booherbg/tedxfargo-charge-sign/docs/img/lens-matrix-clear.png

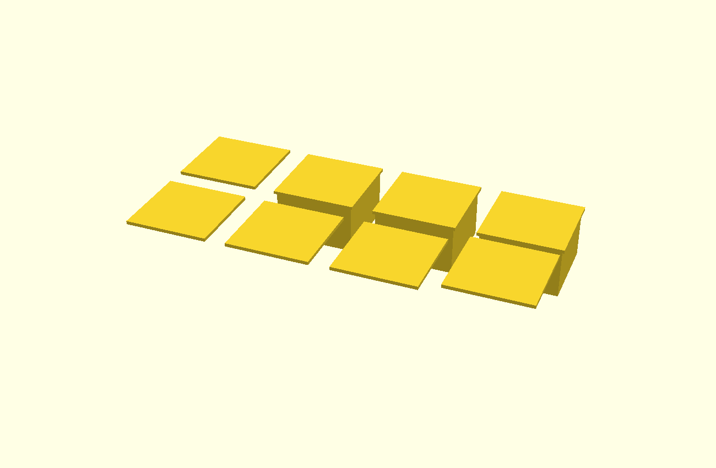
docs/img/lens-matrix-clear.png
