booherbg/tedxfargo-charge-sign/docs/img/lens-matrix-white.png

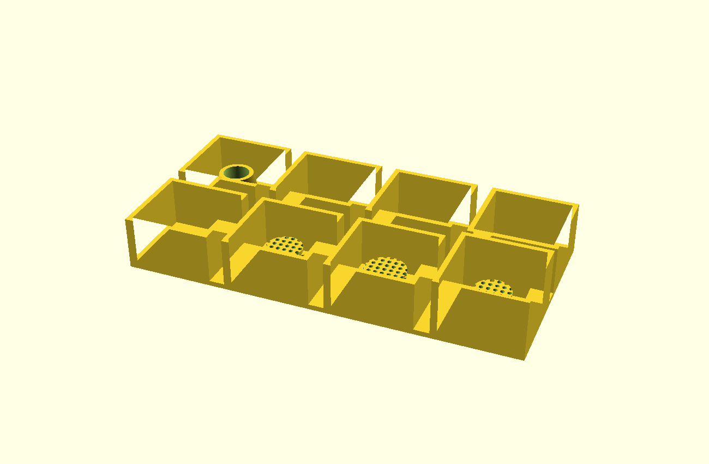
docs/img/lens-matrix-white.png
