booherbg/tedxfargo-charge-sign/docs/img/mockup-cap250-vs-squeezedH.png

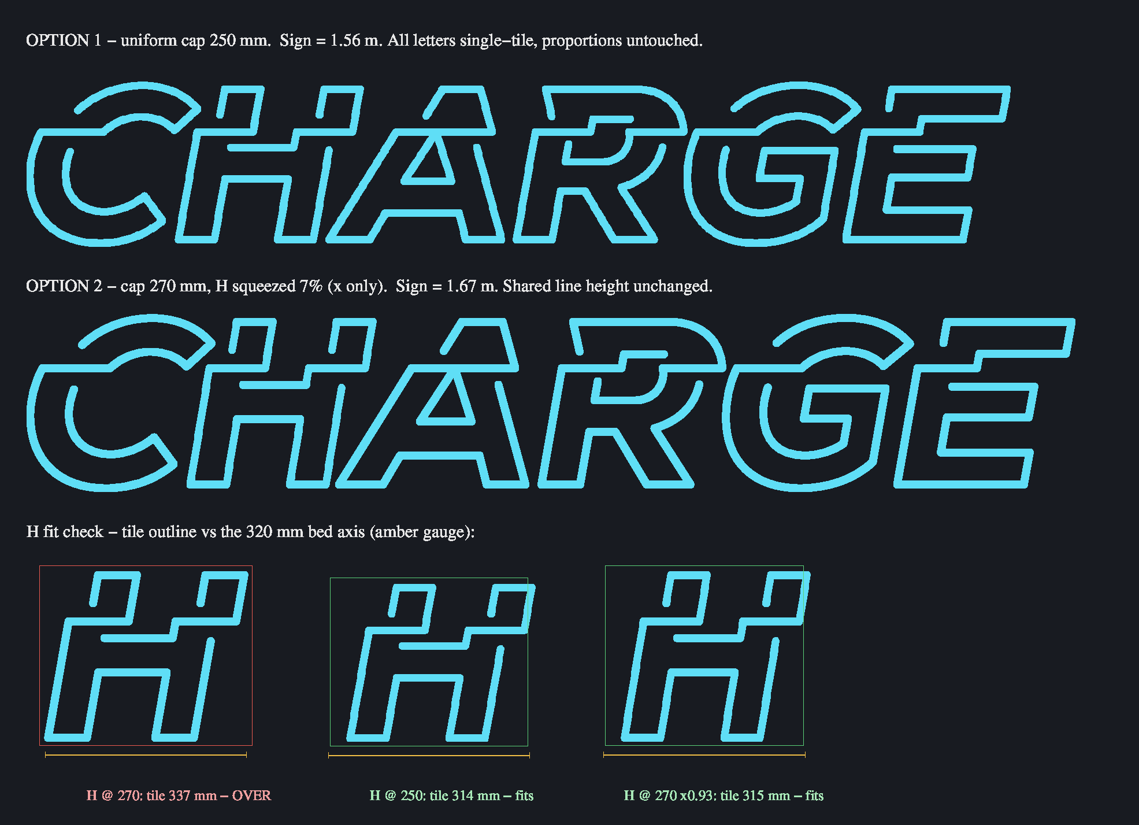
docs/img/mockup-cap250-vs-squeezedH.png
