booherbg/tedxfargo-charge-sign/sign-preview/c_thin.png

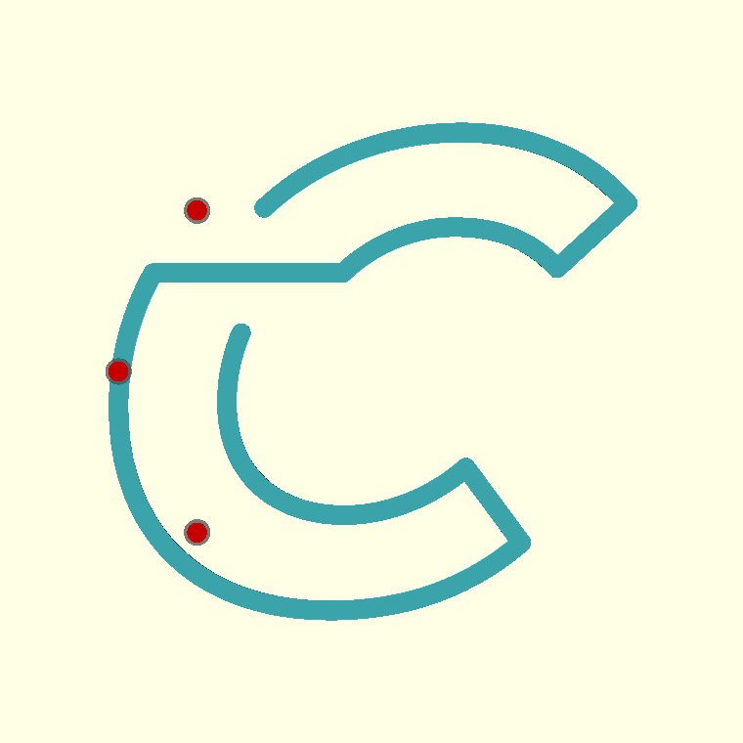
sign-preview/c_thin.png
