booherbg/tedxfargo-charge-sign/sign-preview/charge.png

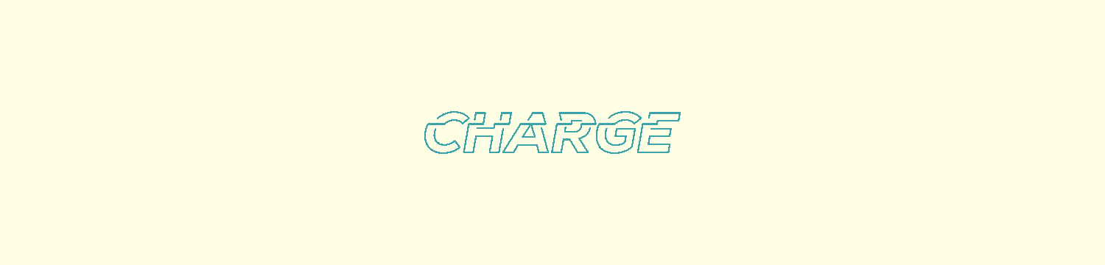
sign-preview/charge.png
