booherbg/tedxfargo-charge-sign/src/parts/bolt2_white.scad

// Integrated bolt v2 — WHITE shell (filament 1). Pair with bolt2_clear -> 3MF.
include <../config.scad>
include <../collar.scad>
include <../bolt.scad>
bolt_shell();
