booherbg/tedxfargo-charge-sign/src/parts/bolt_lens.scad

// Build target: lightning-bolt lens (bolt-shaped diffuser + locating lip).
// Print face-down (flange on bed), lip up; flip in use. Try it in white.
include <../config.scad>
include <../collar.scad>
include <../bolt.scad>
bolt_lens();
