booherbg/tedxfargo-charge-sign/src/parts/bolt_lens_v2_clear.scad

// V2 CLEAR part: clear center stripe + body + lip (edges removed). filament 2.
include <../config.scad>
include <../collar.scad>
include <../bolt.scad>
bolt_lens_v2_clear();
