booherbg/tedxfargo-charge-sign/src/parts/bolt_lens_v2_white.scad

// V2 WHITE part: white EDGES on the viewer/bed face. filament 1.
include <../config.scad>
include <../collar.scad>
include <../bolt.scad>
bolt_lens_v2_white();
