booherbg/tedxfargo-charge-sign/src/parts/bolt_piece.scad

// One element-6 bolt-board plate, one color body. Same cross-section as letters.
//   openscad -D PIECE=<1|2|3|4> -D COL=<1|2|3> -o out.stl src/parts/bolt_piece.scad
//   PIECE: 1 bottom-left, 2 bottom-right, 3 top-left, 4 top-right (bb_plates).
//   COL: 1 black, 2 white, 3 clear.
// CONTINUOUS MODE: channels cross the plate joints (the clip cuts them flush;
// butting plates continue the channel). Pixels/collars are kept off the seams
// by boltboard.py. Fuzz: fuzz_board_global.dat (dead-banded, board-centered).
include <../config.scad>
include <../collar.scad>
include <board_layout.scad>

PIECE = 1;
COL   = 1;

pb_ch_in    = 18;
pb_wall_wh  = 0.8;
pb_wall_bk  = 1.2;
pb_band_out = pb_ch_in + 2*(pb_wall_wh + pb_wall_bk);
pb_liner_t  = 0.4;
pb_wall_h   = dome_clear + 15;
pb_lens_t   = 1.2;
pb_fuse     = 0.1;
pb_seam     = 0.06;
pb_scr_d    = 4.5;
pb_tie_d    = 3.2;

pr = bb_plates[PIECE-1];               // [x0, x1, y0, y1]
x0 = pr[0]; x1 = pr[1]; y0 = pr[2]; y1 = pr[3];
// shave pb_seam off interior edges only (butt-joint clearance)
cx0 = x0 + (x0 > 0.1 ? pb_seam : 0);
cx1 = x1 - (x1 < bb_face[0] - 0.1 ? pb_seam : 0);
cy0 = y0 + (y0 > 0.1 ? pb_seam : 0);
cy1 = y1 - (y1 < bb_face[1] - 0.1 ? pb_seam : 0);

pxs  = [for (p = bb_px)  if (p[0] >= x0 && p[0] < x1 && p[1] >= y0 && p[1] < y1) p];
scrs = [for (p = bb_scr) if (p[0] >= x0 && p[0] < x1 && p[1] >= y0 && p[1] < y1) p];
ties = [for (p = bb_tie) if (p[0] >= x0 && p[0] < x1 && p[1] >= y0 && p[1] < y1) p];
// on-seam pixels (collar lives in the seam strap): Ø13 barrel bite, split
// across the mating plate edges — expanded bounds so BOTH plates cut theirs
bts  = [for (p = bb_bite) if (p[0] >= x0 - 10 && p[0] < x1 + 10
                           && p[1] >= y0 - 10 && p[1] < y1 + 10) p];
pb_bite_d = 13.0;

module path_stroke(pts, w) {
    for (i = [0 : len(pts)-2])
        hull() { translate(pts[i]) circle(d=w); translate(pts[i+1]) circle(d=w); }
}
module band(w) { for (p = bb_paths) path_stroke(p, w); }
module clip() {                       // plate window with seam clearance
    intersection() {
        children(0);
        translate([cx0, cy0, -1]) cube([cx1 - cx0, cy1 - cy0, 60]);
    }
}

module body_black() {
    clip() union() {
        difference() {
            linear_extrude(plate_t) square([bb_face[0], bb_face[1]]);
            for (p = pxs)  translate([p[0], p[1], -0.1]) cylinder(h=plate_t+0.2, d=collar_od);
            for (p = scrs) translate([p[0], p[1], -0.1]) cylinder(h=plate_t+0.2, d=pb_scr_d);
            for (p = ties) translate([p[0], p[1], -0.1]) cylinder(h=plate_t+0.2, d=pb_tie_d);
            for (p = bts)  translate([p[0], p[1], -0.1]) cylinder(h=plate_t+0.2, d=pb_bite_d);
            translate([(x0+x1)/2, y0 + 14, -0.1]) linear_extrude(0.9) mirror([1,0,0])
                text(str("B", PIECE), size=8, halign="center", valign="center");
        }
        translate([0,0,plate_t]) linear_extrude(pb_wall_h)
            difference() { band(pb_band_out); band(pb_band_out - 2*pb_wall_bk); }
    }
}
module body_white() {
    clip() union() {
        difference() {
            translate([0,0,plate_t]) linear_extrude(pb_liner_t) band(pb_ch_in);
            for (p = pxs) translate([p[0], p[1], -0.1])
                cylinder(h=plate_t+pb_liner_t+0.2, d=pixel_through);
            for (p = bts) translate([p[0], p[1], -0.1])
                cylinder(h=plate_t+pb_liner_t+0.2, d=pb_bite_d);
        }
        translate([0,0,plate_t]) linear_extrude(pb_wall_h)
            difference() { band(pb_ch_in + 2*pb_wall_wh); band(pb_ch_in); }
        for (p = pxs) place_collar(p[0], p[1]);
    }
}
module body_clear() {
    z0  = plate_t + pb_wall_h - pb_fuse;
    top = plate_t + pb_wall_h + pb_lens_t;
    // per-plate CROP of the one global fuzz field (identical values -> texture
    // continuous across the joints; cropping keeps surface() meshes small)
    clip() union() {
        translate([0,0,z0]) linear_extrude(top - z0) band(pb_band_out);
        intersection() {
            translate([bb_fuzz_ctr[PIECE-1][0], bb_fuzz_ctr[PIECE-1][1], top-0.1504])
                scale([0.6667,0.6667,1])  // V8: dat sampled at cell/3 = 0.667mm
                surface(file = str("fuzz_board_p", PIECE, ".dat"), center = true, convexity = 8);
            translate([0,0,top-0.3]) linear_extrude(3) band(pb_band_out);
        }
    }
}

if (COL == 1) body_black();
else if (COL == 2) body_white();
else body_clear();
