booherbg/tedxfargo-charge-sign/src/parts/bolt_shell.scad

// Build target: lightning-bolt shell (channel + merged collars). Print rear-down.
include <../config.scad>
include <../collar.scad>
include <../bolt.scad>
bolt_shell();
