booherbg/tedxfargo-charge-sign/src/parts/boltx_data.scad

// AUTO-GENERATED by tools/centerline.py — do not hand-edit
// bolt_element6.pgm @ cap 270mm (ref ): centerline bbox 354.8 x 493.1 mm, tube ~12.3mm wide
// 3 tube segment(s), 1497+370+589 mm, 127 pixels @ 20.0mm pitch
BOLTX_paths = [
    [[10.89,320.45],[11.86,316.57],[12.94,312.72],[14.97,309.29],[17.16,305.95],[19.38,302.62],[21.62,299.31],[23.87,296.00],[26.14,292.71],[28.39,289.40],[30.68,286.12],[32.91,282.80],[35.24,279.55],[37.47,276.24],[39.77,272.97],[42.04,269.67],[44.32,266.38],[46.59,263.10],[48.85,259.80],[51.16,256.53],[53.39,253.22],[55.72,249.96],[57.94,246.64],[60.27,243.39],[62.51,240.07],[64.82,236.81],[67.06,233.50],[69.36,230.23],[71.63,226.94],[73.90,223.64],[76.19,220.37],[78.44,217.06],[80.75,213.80],[83.02,210.51],[85.31,207.23],[87.56,203.92],[89.87,200.66],[92.12,197.35],[94.43,194.09],[96.66,190.77],[98.99,187.52],[101.22,184.20],[103.53,180.94],[105.78,177.63],[107.80,174.20],[108.66,170.32],[107.66,166.45],[105.63,163.02],[103.35,159.73],[101.12,156.41],[98.89,153.10],[96.64,149.79],[94.41,146.47],[92.14,143.17],[89.93,139.84],[87.70,136.52],[85.44,133.23],[83.20,129.92],[80.92,126.62],[78.71,123.30],[76.49,119.97],[74.26,116.65],[72.01,113.34],[69.77,110.03],[67.49,106.74],[65.27,103.42],[63.05,100.09],[60.83,96.76],[58.56,93.47],[56.32,90.16],[54.05,86.87],[51.83,83.54],[49.62,80.21],[47.39,76.89],[45.13,73.58],[42.85,70.30],[40.62,66.99],[38.40,63.66],[36.18,60.33],[33.95,57.01],[31.65,53.74],[29.39,50.44],[27.18,47.11],[24.96,43.78],[22.74,40.45],[20.52,37.12],[18.29,33.81],[16.05,30.49],[13.82,27.17],[11.59,23.86],[9.35,20.54],[7.12,17.23],[4.92,13.88],[2.76,10.51],[1.53,6.74],[0.55,2.87],[2.11,0.00],[6.11,0.00],[10.11,0.00],[14.10,0.00],[18.10,0.00],[22.10,0.00],[26.10,0.00],[30.10,0.00],[34.10,0.00],[38.10,0.00],[42.10,0.00],[46.10,0.00],[50.10,0.00],[54.10,0.00],[58.10,0.00],[62.10,0.00],[66.09,0.00],[70.09,0.00],[74.09,0.00],[78.09,0.00],[82.09,0.00],[86.09,0.00],[90.09,0.00],[94.08,0.25],[98.07,0.28],[102.07,0.28],[106.07,0.28],[110.03,0.69],[113.09,3.10],[115.52,6.28],[117.74,9.60],[119.77,13.05],[121.82,16.48],[123.87,19.92],[125.92,23.35],[127.95,26.79],[130.00,30.23],[132.03,33.67],[134.07,37.11],[136.11,40.55],[138.15,43.99],[140.19,47.43],[142.23,50.87],[144.29,54.30],[146.32,57.75],[148.37,61.18],[150.41,64.62],[152.47,68.05],[154.50,71.50],[156.51,74.95],[158.55,78.39],[160.60,81.83],[162.64,85.26],[164.69,88.70],[166.74,92.13],[169.41,95.02],[173.18,96.05],[176.75,94.36],[179.05,91.13],[181.11,87.70],[183.19,84.29],[185.30,80.88],[187.36,77.46],[189.44,74.04],[191.50,70.61],[193.56,67.19],[195.62,63.76],[197.68,60.33],[199.73,56.90],[201.78,53.47],[203.84,50.04],[205.91,46.61],[207.97,43.19],[210.03,39.76],[212.09,36.33],[214.15,32.90],[216.21,29.48],[218.27,26.05],[220.33,22.62],[222.39,19.19],[224.45,15.76],[226.50,12.33],[228.57,8.91],[230.71,5.53],[233.04,2.28],[236.63,0.78],[240.61,0.55],[244.61,0.55],[248.61,0.55],[252.61,0.55],[256.61,0.55],[260.61,0.55],[264.61,0.55],[268.61,0.55],[272.61,0.55],[276.61,0.55],[280.61,0.55],[284.61,0.55],[288.60,0.55],[292.60,0.55],[296.60,0.55],[300.60,0.55],[304.60,0.55],[308.60,0.55],[312.60,0.55],[316.60,0.55],[320.60,0.55],[324.60,0.55],[328.60,0.55],[332.58,0.78],[336.58,0.83],[340.58,0.83],[344.58,0.83],[348.58,0.83],[352.58,0.84],[354.44,3.65],[353.48,7.53],[352.20,11.29],[350.03,14.64],[347.83,17.99],[345.61,21.31],[343.39,24.64],[341.18,27.97],[338.94,31.28],[336.70,34.60],[334.43,37.89],[332.18,41.19],[329.94,44.51],[327.67,47.80],[325.39,51.09],[323.15,54.40],[320.86,57.68],[318.61,60.99],[316.35,64.28],[314.05,67.56],[311.83,70.88],[309.56,74.17],[307.28,77.46],[305.05,80.78],[302.78,84.07],[300.49,87.35],[298.27,90.68],[296.00,93.97],[293.70,97.24],[291.49,100.57],[289.24,103.87],[286.94,107.15],[284.71,110.47],[282.44,113.76],[280.15,117.04],[277.92,120.36],[275.65,123.65],[273.36,126.93],[271.15,130.26],[268.83,133.52],[266.58,136.83],[264.36,140.15],[262.09,143.44],[259.81,146.72],[257.58,150.05],[255.33,153.35],[253.02,156.62],[250.81,159.95],[248.58,163.27],[246.51,166.68],[245.73,170.58],[246.68,174.44],[248.70,177.88],[250.95,181.18],[253.26,184.45],[255.48,187.77],[257.72,191.08],[260.04,194.34],[262.25,197.67],[264.54,200.95],[266.82,204.24],[269.04,207.56],[271.34,210.84],[273.60,214.13],[275.85,217.44],[278.15,220.71],[280.38,224.03],[282.66,227.31],[284.95,230.60],[287.17,233.92],[289.44,237.21],[291.72,240.50],[293.94,243.82],[296.23,247.10],[298.51,250.39],[300.74,253.71],[303.03,256.98],[305.29,260.28],[307.53,263.60],[309.82,266.88],[312.07,270.18],[314.31,273.49],[316.61,276.76],[318.85,280.08],[321.10,283.38],[323.39,286.67],[325.62,289.98],[327.91,293.26],[330.17,296.56],[332.43,299.86],[334.65,303.18],[336.88,306.51],[339.09,309.84],[341.13,313.26],[342.16,317.12],[343.07,321.01],[340.27,322.79],[336.27,322.79],[332.27,322.79],[328.27,322.79],[324.27,322.79],[320.27,322.79],[316.27,322.79],[312.27,322.79],[308.27,322.79],[304.27,322.79],[300.29,323.07],[296.29,323.07],[292.29,323.07],[288.29,323.11],[284.40,322.66],[281.04,320.65],[278.73,317.39],[276.44,314.11],[274.16,310.82],[271.91,307.51],[269.67,304.20],[267.42,300.89],[265.20,297.57],[262.97,294.25],[260.75,290.92],[258.53,287.60],[256.32,284.27],[254.03,280.99],[251.81,277.66],[249.59,274.33],[247.38,271.00],[245.16,267.67],[242.94,264.35],[240.72,261.02],[238.50,257.70],[236.25,254.39],[234.01,251.08],[231.79,247.75],[229.56,244.43],[227.35,241.10],[225.06,237.82],[222.85,234.48],[220.63,231.16],[218.41,227.83],[216.20,224.50],[213.97,221.18],[211.76,217.85],[209.54,214.52],[207.32,211.19],[205.10,207.87],[202.84,204.57],[200.60,201.25],[198.35,197.95],[196.09,194.65],[193.88,191.31],[191.67,187.99],[189.44,184.66],[187.22,181.33],[184.98,178.02],[182.76,174.70],[180.51,171.39],[178.29,168.07],[176.04,164.76],[173.80,161.44],[171.57,158.13],[169.36,154.79],[167.11,151.48],[164.88,148.17],[162.64,144.86]],
    [[140.38,126.66],[140.65,130.63],[141.04,134.60],[141.69,138.53],[142.59,142.41],[143.56,146.28],[144.47,150.16],[145.41,154.03],[146.33,157.91],[147.27,161.79],[148.20,165.67],[149.12,169.54],[150.01,173.43],[150.87,177.32],[151.83,181.19],[152.74,185.07],[153.67,188.95],[154.59,192.83],[155.52,196.71],[156.43,200.59],[157.37,204.46],[158.29,208.34],[159.25,212.21],[160.14,216.10],[161.10,219.97],[162.02,223.85],[162.93,227.73],[163.87,231.60],[164.81,235.48],[165.72,239.36],[166.64,243.24],[167.61,247.11],[168.53,250.98],[169.45,254.86],[170.39,258.74],[171.32,262.62],[172.23,266.50],[173.15,270.38],[174.11,274.25],[175.00,278.13],[175.92,282.01],[176.83,285.89],[177.70,289.78],[178.65,293.66],[179.55,297.54],[180.43,301.43],[181.39,305.30],[182.32,309.17],[183.04,313.09],[183.44,317.06],[183.00,320.85],[179.32,321.97],[175.33,321.97],[171.35,321.97],[167.36,321.97],[163.37,321.97],[159.38,321.97],[155.40,321.97],[151.41,321.97],[147.42,321.97],[143.44,321.97],[139.45,321.97],[135.46,321.97],[131.47,321.97],[127.49,321.97],[123.50,321.97],[119.51,321.97],[115.53,321.87],[111.55,321.69],[107.56,321.69],[103.58,321.80],[99.60,321.97],[95.62,321.97],[91.63,321.97],[87.64,321.97],[83.65,321.97],[79.67,321.97],[75.71,322.14],[71.79,322.23],[67.81,321.97],[63.82,321.97],[59.84,321.97],[55.85,321.97],[51.86,321.97],[47.88,321.97],[43.89,321.97],[39.90,321.97],[35.91,321.97],[31.93,321.97],[27.94,321.97],[23.95,321.97],[19.97,321.97],[15.98,321.97],[11.99,321.97]],
    [[287.16,324.31],[288.17,328.18],[289.14,332.05],[290.81,335.64],[293.00,338.98],[295.20,342.31],[297.41,345.65],[299.63,348.97],[301.85,352.29],[304.09,355.60],[306.32,358.91],[308.47,362.28],[310.48,365.73],[311.45,369.60],[312.33,373.50],[309.68,375.44],[305.68,375.44],[301.68,375.44],[297.69,375.44],[293.69,375.44],[289.70,375.44],[285.70,375.44],[281.71,375.44],[277.71,375.44],[273.72,375.44],[269.72,375.44],[265.73,375.44],[261.73,375.44],[257.73,375.44],[253.74,375.44],[249.74,375.44],[245.75,375.44],[241.75,375.44],[237.77,375.17],[233.78,375.17],[229.78,375.17],[225.79,375.17],[221.80,375.29],[220.68,378.46],[221.57,382.36],[222.67,386.18],[224.67,389.64],[226.71,393.07],[228.76,396.50],[230.81,399.93],[232.86,403.36],[234.90,406.79],[236.95,410.22],[238.99,413.66],[241.01,417.10],[243.05,420.54],[245.10,423.97],[247.16,427.39],[249.22,430.82],[251.26,434.25],[253.31,437.68],[255.37,441.11],[257.41,444.54],[259.46,447.97],[261.50,451.40],[263.56,454.83],[265.60,458.26],[267.62,461.71],[269.68,465.13],[271.67,468.60],[273.73,472.02],[275.76,475.46],[277.82,478.89],[279.78,482.36],[280.84,486.20],[281.76,490.09],[280.42,493.07],[276.42,493.15],[272.43,493.15],[268.43,493.15],[264.44,493.15],[260.44,493.15],[256.45,493.15],[252.45,493.15],[248.46,493.15],[244.46,493.15],[240.47,493.15],[236.47,493.15],[232.47,493.15],[228.48,493.15],[224.48,493.15],[220.49,493.15],[216.49,493.15],[212.50,493.15],[208.50,493.15],[204.51,493.15],[200.51,493.15],[196.52,493.15],[192.52,493.15],[188.52,493.15],[184.53,493.15],[180.53,493.15],[176.54,493.15],[172.54,493.14],[168.57,492.83],[164.70,491.89],[162.01,489.12],[160.08,485.62],[158.16,482.12],[156.25,478.61],[154.35,475.10],[152.44,471.59],[150.52,468.08],[148.59,464.59],[146.69,461.07],[144.75,457.58],[142.86,454.06],[140.96,450.54],[139.03,447.05],[137.13,443.53],[135.23,440.02],[133.30,436.52],[131.40,433.00],[129.48,429.50],[127.57,425.99],[125.66,422.48],[123.74,418.98],[121.83,415.47],[119.93,411.96],[118.02,408.44],[116.10,404.94],[114.19,401.43],[112.27,397.93],[110.36,394.42],[108.45,390.91],[106.53,387.41],[104.62,383.90],[102.71,380.39],[100.80,376.88],[98.90,373.36],[96.98,369.86],[95.08,366.34],[93.17,362.84],[91.27,359.32],[89.36,355.82],[87.43,352.32],[85.53,348.80],[83.63,345.29],[81.73,341.77],[79.84,338.25],[77.97,334.72],[76.55,331.01],[75.66,327.12],[74.84,323.21]]
];
BOLTX_closed = [0, 0, 0];
BOLTX_pixels = [[10.89,320.45],[19.38,302.62],[30.68,286.12],[42.04,269.67],[53.39,253.22],[64.82,236.81],[76.19,220.37],[87.56,203.92],[98.99,187.52],[108.66,170.32],[98.89,153.10],[87.70,136.52],[76.49,119.97],[65.27,103.42],[54.05,86.87],[42.85,70.30],[31.65,53.74],[20.52,37.12],[9.35,20.54],[0.55,2.87],[18.10,0.00],[38.10,0.00],[58.10,0.00],[78.09,0.00],[98.07,0.28],[115.52,6.28],[125.92,23.35],[136.11,40.55],[146.32,57.75],[156.51,74.95],[166.74,92.13],[181.11,87.70],[191.50,70.61],[201.78,53.47],[212.09,36.33],[222.39,19.19],[233.04,2.28],[252.61,0.55],[272.61,0.55],[292.60,0.55],[312.60,0.55],[332.58,0.78],[352.58,0.84],[347.83,17.99],[336.70,34.60],[325.39,51.09],[314.05,67.56],[302.78,84.07],[291.49,100.57],[280.15,117.04],[268.83,133.52],[257.58,150.05],[246.51,166.68],[253.26,184.45],[264.54,200.95],[275.85,217.44],[287.17,233.92],[298.51,250.39],[309.82,266.88],[321.10,283.38],[332.43,299.86],[342.16,317.12],[328.27,322.79],[308.27,322.79],[288.29,323.11],[274.16,310.82],[262.97,294.25],[251.81,277.66],[240.72,261.02],[229.56,244.43],[218.41,227.83],[207.32,211.19],[196.09,194.65],[184.98,178.02],[173.80,161.44],[162.64,144.86],[140.38,126.66],[143.47,145.87],[147.99,164.85],[152.43,183.86],[156.97,202.83],[161.52,221.81],[166.09,240.78],[170.63,259.76],[175.16,278.74],[179.60,297.74],[183.42,316.85],[167.99,321.97],[148.47,321.97],[128.96,321.97],[109.45,321.69],[89.95,321.97],[70.54,322.08],[51.02,321.97],[31.51,321.97],[11.99,321.97],[287.16,324.31],[295.06,342.09],[306.02,358.48],[310.47,375.40],[290.76,375.44],[271.05,375.44],[251.34,375.44],[231.65,375.17],[221.96,384.18],[231.63,401.30],[241.70,418.24],[251.80,435.17],[261.91,452.09],[271.94,469.06],[280.90,486.46],[268.43,493.15],[248.72,493.15],[229.01,493.15],[209.30,493.15],[189.59,493.15],[169.90,492.90],[157.02,480.01],[147.59,462.71],[138.14,445.41],[128.72,428.10],[119.30,410.78],[109.85,393.49],[100.42,376.18],[91.02,358.85],[81.60,341.54],[74.84,323.21]];
BOLTX_bbox = [354.77, 493.15];
