booherbg/tedxfargo-charge-sign/src/parts/cap_fit_0p1.scad

// Fit test: over-cap skirt clearance 0.1mm (2 dots). Middle.
include <../config.scad>
include <../collar.scad>
include <../bolt.scad>
cap_chunk(0.1, 2);
