booherbg/tedxfargo-charge-sign/src/parts/cap_fit_0p2.scad

// Fit test: over-cap skirt clearance 0.2mm (1 dot). Loosest of the three.
include <../config.scad>
include <../collar.scad>
include <../bolt.scad>
cap_chunk(0.2, 1);
