booherbg/tedxfargo-charge-sign/src/parts/collar_harness.scad

// Build target: collar A/B test tile (original vs chamfered v2).
include <../config.scad>
include <../collar.scad>
include <../collar_v2.scad>
include <../harness.scad>
collar_harness();
