booherbg/tedxfargo-charge-sign/src/parts/coupon_body.scad

// Build target: the stackup test coupon body.
include <../config.scad>
include <../collar.scad>
include <../diffuser.scad>
include <../coupon.scad>
coupon_body();
