booherbg/tedxfargo-charge-sign/src/parts/lens_fit_0p2.scad

// Fit test: inner-lens lip clearance 0.2mm (3 dots).
include <../config.scad>
include <../collar.scad>
include <../bolt.scad>
lens_chunk(0.2, 3, label="0.2");
