booherbg/tedxfargo-charge-sign/src/parts/lens_fit_0p3.scad

// Fit test: inner-lens lip clearance 0.3mm (2 dots).
include <../config.scad>
include <../collar.scad>
include <../bolt.scad>
lens_chunk(0.3, 2, label="0.3");
