booherbg/tedxfargo-charge-sign/src/parts/letter_C_data.scad

// AUTO-GENERATED by tools/centerline.py — do not hand-edit
// C.eps @ cap 270mm (ref H.eps): centerline bbox 285.9 x 270.9 mm, tube ~11.8mm wide
// 1 tube segment(s), 1161 mm, 69 pixels @ 17.0mm pitch
C_paths = [
    [[85.59,231.18],[88.75,233.62],[91.83,236.17],[94.99,238.61],[98.24,240.94],[101.55,243.17],[104.83,245.46],[108.27,247.48],[111.75,249.45],[115.22,251.42],[118.76,253.28],[122.29,255.15],[125.94,256.76],[129.60,258.37],[133.31,259.85],[137.10,261.13],[140.93,262.27],[144.72,263.53],[148.56,264.65],[152.39,265.78],[156.26,266.75],[160.16,267.61],[164.11,268.20],[168.06,268.85],[172.02,269.37],[175.97,269.95],[179.93,270.41],[183.90,270.76],[187.89,270.88],[191.88,270.88],[195.88,270.88],[199.88,270.88],[203.87,270.84],[207.84,270.42],[211.80,269.88],[215.74,269.29],[219.70,268.79],[223.62,268.09],[227.49,267.10],[231.38,266.15],[235.25,265.16],[239.02,263.84],[242.82,262.61],[246.52,261.12],[250.14,259.42],[253.75,257.72],[257.31,255.90],[260.73,253.85],[264.15,251.78],[267.51,249.62],[270.70,247.21],[273.86,244.77],[276.98,242.26],[279.99,239.64],[282.85,236.85],[284.95,233.53],[285.38,229.66],[283.75,226.06],[280.77,223.41],[277.88,220.64],[274.90,217.99],[271.97,215.28],[269.04,212.57],[266.06,209.91],[263.18,207.15],[260.16,204.53],[257.29,201.74],[254.28,199.12],[250.70,197.44],[246.78,197.49],[243.25,199.26],[240.23,201.88],[237.00,204.23],[233.67,206.42],[230.18,208.38],[226.65,210.25],[222.96,211.79],[219.20,213.13],[215.36,214.24],[211.51,215.31],[207.56,215.89],[203.61,216.46],[199.66,217.06],[195.66,217.06],[191.68,217.30],[187.71,217.06],[183.72,217.06],[179.76,216.53],[175.80,215.96],[171.87,215.26],[167.98,214.37],[164.17,213.18],[160.36,212.00],[156.66,210.49],[152.97,208.96],[149.41,207.15],[145.93,205.18],[142.51,203.12],[139.19,200.89],[135.94,198.56],[132.74,196.18],[129.66,193.64],[126.03,192.03],[122.10,191.47],[118.10,191.47],[114.10,191.47],[110.10,191.47],[106.11,191.47],[102.11,191.47],[98.11,191.47],[94.12,191.47],[90.12,191.47],[86.12,191.47],[82.13,191.47],[78.13,191.47],[74.13,191.47],[70.14,191.47],[66.14,191.47],[62.14,191.47],[58.14,191.47],[54.15,191.47],[50.15,191.47],[46.15,191.47],[42.16,191.47],[38.16,191.47],[34.16,191.47],[30.17,191.47],[26.17,191.47],[22.22,190.97],[18.70,189.26],[16.70,185.82],[14.94,182.23],[13.29,178.59],[11.72,174.92],[10.29,171.20],[9.07,167.39],[7.75,163.62],[6.50,159.83],[5.40,155.99],[4.39,152.12],[3.57,148.21],[2.83,144.28],[2.13,140.35],[1.59,136.39],[0.97,132.45],[0.44,128.49],[0.11,124.52],[0.00,120.53],[0.00,116.53],[0.00,112.53],[0.00,108.54],[0.40,104.57],[0.63,100.59],[1.14,96.63],[1.67,92.68],[2.23,88.74],[3.02,84.83],[3.86,80.92],[5.03,77.10],[6.28,73.30],[7.56,69.51],[8.84,65.73],[10.39,62.05],[12.13,58.45],[13.93,54.88],[15.92,51.42],[17.93,47.96],[20.32,44.76],[22.72,41.57],[25.16,38.41],[27.94,35.54],[30.56,32.52],[33.39,29.70],[36.41,27.08],[39.44,24.48],[42.66,22.12],[46.00,19.92],[49.36,17.76],[52.83,15.79],[56.39,13.98],[59.98,12.22],[63.61,10.55],[67.33,9.07],[71.05,7.63],[74.85,6.38],[78.70,5.31],[82.60,4.43],[86.50,3.59],[90.41,2.74],[94.34,2.03],[98.30,1.46],[102.25,0.99],[106.25,0.82],[110.21,0.44],[114.17,0.00],[118.17,0.00],[122.17,0.00],[126.16,0.00],[130.12,0.44],[134.09,0.81],[138.07,1.06],[142.04,1.45],[146.00,1.86],[149.95,2.46],[153.87,3.24],[157.78,4.08],[161.69,4.90],[165.60,5.74],[169.45,6.78],[173.29,7.90],[177.10,9.08],[180.81,10.56],[184.53,12.05],[188.20,13.61],[191.90,15.12],[195.49,16.88],[199.05,18.69],[202.61,20.50],[206.02,22.58],[209.38,24.75],[212.80,26.82],[216.09,29.08],[219.37,31.37],[222.54,33.80],[225.08,36.84],[225.26,40.74],[223.98,44.49],[221.54,47.65],[219.20,50.89],[216.80,54.09],[214.39,57.28],[212.09,60.54],[209.69,63.74],[207.29,66.93],[204.94,70.16],[202.56,73.38],[199.99,76.41],[196.23,77.62],[192.36,76.70],[188.99,74.62],[185.70,72.35],[182.36,70.16],[178.86,68.23],[175.33,66.37],[171.75,64.59],[168.15,62.85],[164.42,61.43],[160.67,60.03],[156.92,58.65],[153.06,57.63],[149.16,56.74],[145.24,56.02],[141.34,55.17],[137.37,54.75],[133.39,54.48],[129.41,54.26],[125.42,54.26],[121.45,54.64],[117.46,54.72],[113.52,55.38],[109.60,56.17],[105.70,57.04],[101.87,58.16],[98.15,59.63],[94.48,61.20],[90.92,63.01],[87.49,65.06],[84.23,67.35],[81.11,69.86],[78.24,72.64],[75.43,75.48],[72.99,78.64],[70.85,82.01],[68.88,85.49],[67.04,89.03],[65.60,92.76],[64.49,96.59],[63.35,100.41],[62.62,104.34],[62.07,108.29],[61.76,112.26],[61.48,116.23],[61.71,120.19],[61.76,124.18],[62.05,128.16],[62.64,132.11],[63.18,136.07],[63.94,139.99],[64.95,143.86],[66.03,147.70],[67.28,151.50],[68.53,155.29]]
];
C_closed = [0];
C_pixels = [[85.59,231.18],[99.16,241.56],[113.71,250.52],[129.01,258.10],[145.17,263.68],[161.73,267.85],[178.65,270.26],[195.70,270.88],[212.72,269.72],[229.50,266.64],[245.78,261.48],[260.97,253.67],[274.96,243.88],[285.56,231.09],[275.15,218.24],[262.61,206.63],[248.85,197.14],[234.48,205.85],[219.09,213.16],[202.39,216.66],[185.36,217.06],[168.47,214.57],[152.45,208.69],[137.81,199.89],[123.27,191.50],[106.17,191.47],[89.06,191.47],[71.96,191.47],[54.85,191.47],[37.75,191.47],[20.75,190.56],[12.23,176.17],[6.57,160.05],[2.66,143.42],[0.40,126.49],[0.00,109.42],[1.72,92.45],[5.44,75.81],[11.46,59.82],[20.07,45.09],[31.06,32.03],[44.18,21.12],[59.02,12.66],[74.90,6.36],[91.56,2.51],[108.51,0.49],[125.58,0.00],[142.56,1.51],[159.38,4.44],[175.95,8.64],[191.80,15.07],[206.88,23.10],[221.08,32.62],[222.00,47.04],[211.88,60.83],[201.67,74.54],[186.87,73.13],[172.01,64.71],[156.13,58.43],[139.40,55.06],[122.38,54.49],[105.53,57.07],[89.78,63.62],[76.54,74.34],[67.24,88.60],[62.59,104.98],[61.76,121.95],[63.69,138.90],[68.53,155.29]];
C_bbox = [285.88, 270.88];
