booherbg/tedxfargo-charge-sign/src/parts/lid_0p6mm.scad

// Build target: 0.6mm flanged-plug lid — thinnest practical face; let infill /
// a white layer do the diffusing. Plug keeps the thin face rigid.
include <../config.scad>
include <../diffuser.scad>
diffuser_lid(0.6);
