booherbg/tedxfargo-charge-sign/src/parts/lid_1mm.scad

// Build target: 1mm flanged-plug diffuser lid.
include <../config.scad>
include <../diffuser.scad>
diffuser_lid(1);
