booherbg/tedxfargo-charge-sign/src/parts/lid_2mm.scad

// Build target: 2mm flanged-plug diffuser lid.
include <../config.scad>
include <../diffuser.scad>
diffuser_lid(2);
