booherbg/tedxfargo-charge-sign/src/parts/lid_3mm.scad

// Build target: 3mm flanged-plug diffuser lid.
include <../config.scad>
include <../diffuser.scad>
diffuser_lid(3);
