booherbg/tedxfargo-charge-sign/src/parts/matrix_clear.scad

// CLEAR optic of the lit-cell test matrix -> nozzle/filament 2 (clear PETG).
// Co-registered with matrix_white (same origin). Print plate-down.
include <../config.scad>
include <../collar.scad>
include <../lens_cell.scad>
matrix_clear();
