booherbg/tedxfargo-charge-sign/src/parts/matrix_white.scad

// WHITE body of the lit-cell test matrix -> nozzle/filament 1 (white PETG).
// Co-registered with matrix_clear (same origin). Print plate-down.
include <../config.scad>
include <../collar.scad>
include <../lens_cell.scad>
matrix_white();
