booherbg/tedxfargo-charge-sign/src/parts/panel_1mm.scad

// Build target: 1mm diffuser panel.
include <../config.scad>
include <../diffuser.scad>
diffuser_panel(1);
