booherbg/tedxfargo-charge-sign/src/parts/panel_2mm.scad

// Build target: 2mm diffuser panel.
include <../config.scad>
include <../diffuser.scad>
diffuser_panel(2);
