booherbg/tedxfargo-charge-sign/src/parts/panel_3mm.scad

// Build target: 3mm diffuser panel.
include <../config.scad>
include <../diffuser.scad>
diffuser_panel(3);
