booherbg/tedxfargo-charge-sign/src/parts/testbox_clear.scad

// CLEAR integrated lens roof of the test box (fuzzy-skin this, print lens-up). filament 2.
include <../config.scad>
include <../collar.scad>
include <../testbox.scad>
testbox_clear();
