booherbg/tedxfargo-charge-sign/src/parts/testbox_white.scad

// WHITE shell of the 5-LED stroke test box (plate + walls + collars). filament 1.
include <../config.scad>
include <../collar.scad>
include <../testbox.scad>
testbox_white();
