booherbg/tedxfargo-charge-sign/src/parts/word_data.scad

// AUTO-GENERATED by tools/centerline.py — do not hand-edit
// CHARGE.eps @ cap 250mm (ref H.eps): centerline bbox 1556.4 x 251.2 mm, tube ~11.2mm wide
// 10 tube segment(s), 1350+1375+1033+371+154+949+964+651+183+535 mm, 457 pixels @ 17.0mm pitch
WORD_paths = [
    [[1368.46,216.09],[1369.21,220.02],[1369.94,223.95],[1370.58,227.89],[1371.31,231.82],[1371.99,235.75],[1372.69,239.68],[1373.60,243.55],[1376.99,245.25],[1380.96,245.51],[1384.96,245.51],[1388.95,245.51],[1392.95,245.51],[1396.94,245.51],[1400.94,245.51],[1404.93,245.51],[1408.93,245.51],[1412.92,245.51],[1416.92,245.51],[1420.91,245.51],[1424.91,245.51],[1428.90,245.51],[1432.90,245.51],[1436.89,245.51],[1440.89,245.51],[1444.88,245.51],[1448.88,245.51],[1452.87,245.51],[1456.87,245.51],[1460.86,245.51],[1464.86,245.51],[1468.85,245.51],[1472.85,245.51],[1476.84,245.51],[1480.84,245.51],[1484.83,245.51],[1488.83,245.51],[1492.82,245.51],[1496.82,245.51],[1500.81,245.51],[1504.81,245.51],[1508.80,245.51],[1512.80,245.51],[1516.79,245.51],[1520.79,245.51],[1524.78,245.51],[1528.78,245.51],[1532.77,245.51],[1536.77,245.51],[1540.76,245.51],[1544.76,245.51],[1548.75,245.51],[1552.75,245.47],[1556.16,243.96],[1555.97,240.01],[1555.70,236.04],[1555.00,232.11],[1554.29,228.18],[1553.56,224.25],[1552.83,220.32],[1552.10,216.40],[1551.40,212.46],[1550.69,208.53],[1549.99,204.60],[1549.08,200.71],[1545.98,198.68],[1542.00,198.53],[1538.01,198.53],[1534.01,198.53],[1530.02,198.53],[1526.02,198.53],[1522.03,198.53],[1518.03,198.53],[1514.04,198.53],[1510.04,198.53],[1506.05,198.53],[1502.05,198.53],[1498.06,198.53],[1494.06,198.53],[1490.07,198.53],[1486.07,198.53],[1482.08,198.53],[1478.08,198.53],[1474.09,198.53],[1470.09,198.53],[1466.10,198.53],[1462.10,198.53],[1458.11,198.53],[1454.11,198.53],[1450.12,198.53],[1446.12,198.53],[1442.13,198.53],[1438.13,198.53],[1434.14,198.53],[1430.14,198.53],[1426.15,198.50],[1422.27,197.62],[1420.61,194.15],[1419.87,190.23],[1419.20,186.29],[1418.50,182.36],[1417.22,178.66],[1413.62,177.29],[1409.62,177.29],[1405.63,177.29],[1401.63,177.29],[1397.64,177.29],[1393.64,177.29],[1389.65,177.29],[1385.65,177.29],[1381.66,177.29],[1377.66,177.29],[1373.67,177.29],[1369.67,177.29],[1365.68,177.29],[1361.68,177.29],[1357.69,177.29],[1353.69,177.29],[1349.70,177.29],[1345.70,177.29],[1341.71,177.29],[1337.71,177.29],[1333.74,176.98],[1330.20,175.46],[1329.30,171.58],[1328.57,167.66],[1327.92,163.72],[1327.19,159.79],[1326.51,155.86],[1325.81,151.92],[1325.11,147.99],[1324.42,144.06],[1323.77,140.12],[1323.04,136.19],[1322.37,132.25],[1321.66,128.32],[1320.96,124.39],[1320.28,120.45],[1319.55,116.53],[1318.89,112.59],[1318.16,108.66],[1317.51,104.72],[1316.81,100.79],[1316.13,96.85],[1315.40,92.93],[1314.77,88.98],[1314.05,85.05],[1313.36,81.12],[1312.66,77.19],[1312.01,73.25],[1311.27,69.32],[1310.62,65.38],[1309.92,61.45],[1309.22,57.52],[1308.51,53.59],[1307.81,49.66],[1307.18,45.71],[1306.48,41.78],[1305.77,37.85],[1305.07,33.92],[1304.40,29.98],[1303.67,26.05],[1303.03,22.11],[1302.30,18.18],[1301.80,14.23],[1301.47,10.26],[1301.93,6.46],[1305.70,5.72],[1309.69,5.72],[1313.69,5.72],[1317.68,5.72],[1321.68,5.72],[1325.67,5.72],[1329.67,5.72],[1333.66,5.72],[1337.66,5.72],[1341.65,5.72],[1345.65,5.72],[1349.64,5.72],[1353.64,5.72],[1357.63,5.72],[1361.63,5.72],[1365.62,5.72],[1369.62,5.72],[1373.61,5.72],[1377.61,5.72],[1381.60,5.72],[1385.60,5.72],[1389.59,5.72],[1393.59,5.72],[1397.58,5.72],[1401.58,5.72],[1405.57,5.72],[1409.57,5.72],[1413.56,5.72],[1417.56,5.72],[1421.55,5.72],[1425.55,5.72],[1429.54,5.72],[1433.54,5.72],[1437.53,5.72],[1441.53,5.72],[1445.52,5.72],[1449.52,5.72],[1453.51,5.72],[1457.51,5.72],[1461.50,5.72],[1465.50,5.72],[1469.49,5.72],[1473.49,5.72],[1477.48,5.72],[1481.48,5.72],[1485.41,6.16],[1487.55,9.23],[1488.28,13.16],[1489.01,17.09],[1489.74,21.01],[1490.45,24.94],[1491.15,28.87],[1491.86,32.81],[1492.56,36.74],[1493.26,40.67],[1493.87,44.61],[1494.19,48.59],[1493.41,52.25],[1489.56,53.10],[1485.57,53.10],[1481.57,53.10],[1477.58,53.10],[1473.58,53.10],[1469.59,53.10],[1465.59,53.10],[1461.60,53.10],[1457.60,53.10],[1453.61,53.10],[1449.61,53.10],[1445.62,53.10],[1441.62,53.10],[1437.63,53.10],[1433.63,53.10],[1429.64,53.10],[1425.64,53.10],[1421.65,53.10],[1417.65,53.10],[1413.66,53.10],[1409.66,53.10],[1405.67,53.10],[1401.67,53.10],[1397.68,53.10],[1393.68,53.10],[1389.69,53.10],[1385.69,53.10],[1381.70,53.10],[1377.70,53.10],[1373.71,53.10],[1369.71,53.10],[1366.13,54.20],[1366.01,58.07],[1366.32,62.04],[1366.82,66.00],[1367.49,69.93],[1368.13,73.88],[1368.85,77.80],[1369.52,81.74],[1370.16,85.68],[1370.89,89.61],[1371.56,93.55],[1372.19,97.49],[1372.95,101.41],[1375.55,104.11],[1379.49,104.58],[1383.49,104.58],[1387.48,104.58],[1391.48,104.58],[1395.47,104.58],[1399.47,104.58],[1403.47,104.58],[1407.46,104.58],[1411.46,104.58],[1415.45,104.58],[1419.45,104.58],[1423.44,104.58],[1427.44,104.58],[1431.43,104.58],[1435.43,104.58],[1439.42,104.58],[1443.42,104.58],[1447.41,104.58],[1451.41,104.58],[1455.40,104.58],[1459.40,104.58],[1463.39,104.58],[1467.39,104.58],[1471.38,104.58],[1475.38,104.58],[1479.37,104.58],[1483.37,104.58],[1487.36,104.58],[1491.34,104.74],[1494.37,106.85],[1495.19,110.75],[1495.92,114.68],[1496.65,118.61],[1497.38,122.53],[1498.09,126.46],[1498.79,130.39],[1499.50,134.32],[1500.20,138.26],[1500.82,142.19],[1501.20,146.16],[1499.78,149.46],[1495.85,149.92],[1491.85,149.92],[1487.86,149.92],[1483.86,149.92],[1479.87,149.92],[1475.87,149.92],[1471.88,149.92],[1467.88,149.92],[1463.89,149.92],[1459.89,149.92],[1455.90,149.92],[1451.90,149.92],[1447.91,149.92],[1443.91,149.92],[1439.92,149.92],[1435.92,149.92],[1431.93,149.92],[1427.93,149.92],[1423.94,149.92],[1419.94,149.92],[1415.95,149.92],[1411.95,149.92],[1407.96,149.92],[1403.96,149.92],[1399.97,149.92],[1395.97,149.92],[1391.98,149.92],[1387.98,149.92],[1383.99,149.92]],
    [[1144.61,230.66],[1148.12,232.58],[1151.67,234.43],[1155.16,236.39],[1158.83,238.00],[1162.52,239.55],[1166.23,241.06],[1170.04,242.30],[1173.85,243.52],[1177.69,244.65],[1181.53,245.78],[1185.40,246.82],[1189.30,247.70],[1193.25,248.40],[1197.21,248.96],[1201.16,249.61],[1205.13,250.00],[1209.09,250.52],[1213.08,250.82],[1217.06,251.17],[1221.06,251.23],[1225.06,251.23],[1229.06,251.23],[1233.07,251.23],[1237.04,250.82],[1241.02,250.49],[1244.98,249.95],[1248.95,249.43],[1252.91,248.85],[1256.84,248.13],[1260.73,247.18],[1264.61,246.19],[1268.46,245.07],[1272.26,243.81],[1276.05,242.52],[1279.79,241.08],[1283.40,239.35],[1287.05,237.72],[1290.56,235.79],[1293.95,233.66],[1297.28,231.44],[1300.61,229.21],[1303.93,226.97],[1307.14,224.58],[1310.16,221.95],[1313.07,219.20],[1315.26,215.92],[1315.73,212.06],[1313.80,208.62],[1310.72,206.06],[1307.63,203.51],[1304.55,200.96],[1301.46,198.41],[1298.37,195.87],[1295.29,193.31],[1292.20,190.76],[1289.11,188.21],[1286.02,185.66],[1282.65,183.56],[1278.74,183.15],[1275.15,184.81],[1271.99,187.26],[1268.71,189.56],[1265.38,191.79],[1261.90,193.76],[1258.32,195.55],[1254.59,196.98],[1250.79,198.27],[1246.96,199.43],[1243.08,200.42],[1239.13,201.02],[1235.16,201.58],[1231.19,202.10],[1227.20,202.21],[1223.19,202.21],[1219.19,202.21],[1215.22,201.78],[1211.24,201.39],[1207.29,200.77],[1203.34,200.14],[1199.47,199.13],[1195.61,198.07],[1191.76,196.95],[1188.00,195.59],[1184.31,194.04],[1180.74,192.22],[1177.22,190.32],[1173.80,188.25],[1170.47,186.02],[1167.23,183.66],[1164.06,181.22],[1160.90,178.77],[1157.13,177.51],[1153.14,177.29],[1149.13,177.29],[1145.13,177.29],[1141.12,177.29],[1137.12,177.29],[1133.12,177.29],[1129.11,177.29],[1125.11,177.29],[1121.10,177.29],[1117.10,177.29],[1113.09,177.29],[1109.09,177.29],[1105.08,177.29],[1101.08,177.29],[1097.07,177.29],[1093.07,177.29],[1089.06,177.29],[1085.06,177.29],[1081.05,177.29],[1077.05,177.29],[1073.05,177.29],[1069.04,177.29],[1065.10,176.61],[1062.08,174.22],[1060.48,170.56],[1058.98,166.84],[1057.56,163.10],[1056.23,159.32],[1055.15,155.47],[1053.97,151.64],[1052.85,147.80],[1051.85,143.92],[1051.06,140.00],[1050.49,136.03],[1049.84,132.08],[1049.12,128.14],[1048.61,124.17],[1048.20,120.20],[1047.89,116.22],[1047.79,112.22],[1047.55,108.24],[1047.39,104.24],[1047.67,100.26],[1047.79,96.27],[1047.87,92.27],[1048.35,88.29],[1048.95,84.34],[1049.48,80.37],[1050.16,76.43],[1051.14,72.55],[1052.25,68.70],[1053.39,64.87],[1054.67,61.07],[1056.14,57.35],[1057.79,53.70],[1059.66,50.16],[1061.69,46.71],[1063.73,43.26],[1065.99,39.96],[1068.38,36.75],[1070.91,33.65],[1073.61,30.69],[1076.40,27.82],[1079.42,25.19],[1082.49,22.62],[1085.68,20.21],[1089.06,18.05],[1092.43,15.89],[1095.87,13.85],[1099.45,12.04],[1103.07,10.34],[1106.79,8.87],[1110.54,7.47],[1114.29,6.07],[1118.13,4.95],[1122.05,4.10],[1125.96,3.28],[1129.88,2.45],[1133.82,1.72],[1137.79,1.23],[1141.76,0.83],[1145.75,0.59],[1149.73,0.20],[1153.72,0.00],[1157.72,0.00],[1161.73,0.00],[1165.70,0.41],[1169.68,0.67],[1173.66,1.06],[1177.65,1.28],[1181.61,1.76],[1185.58,2.31],[1189.50,3.10],[1193.42,3.92],[1197.35,4.71],[1201.27,5.52],[1205.15,6.50],[1208.99,7.63],[1212.81,8.82],[1216.58,10.16],[1220.31,11.63],[1224.00,13.18],[1227.70,14.71],[1231.36,16.33],[1234.89,18.22],[1238.45,20.06],[1241.89,22.10],[1245.23,24.30],[1248.56,26.52],[1251.88,28.76],[1255.16,31.07],[1258.29,33.56],[1261.36,36.13],[1263.74,39.28],[1264.83,43.12],[1265.58,47.06],[1266.25,51.00],[1266.95,54.94],[1267.62,58.89],[1268.29,62.84],[1268.99,66.78],[1269.67,70.73],[1270.33,74.68],[1271.03,78.62],[1271.72,82.56],[1272.45,86.50],[1273.07,90.45],[1273.78,94.39],[1274.49,98.33],[1275.12,102.29],[1275.83,106.23],[1276.52,110.17],[1277.16,114.12],[1277.88,118.06],[1278.56,122.01],[1279.27,125.95],[1279.92,129.90],[1280.61,133.84],[1281.31,137.78],[1281.53,141.77],[1281.74,145.73],[1278.41,147.43],[1274.41,147.47],[1270.40,147.47],[1266.40,147.47],[1262.40,147.47],[1258.39,147.47],[1254.39,147.47],[1250.38,147.47],[1246.38,147.47],[1242.37,147.47],[1238.37,147.47],[1234.36,147.47],[1230.36,147.47],[1226.35,147.47],[1222.35,147.47],[1218.34,147.47],[1214.34,147.47],[1210.33,147.47],[1206.33,147.47],[1202.33,147.47],[1198.32,147.47],[1194.32,147.47],[1190.31,147.47],[1186.31,147.47],[1182.30,147.47],[1178.30,147.47],[1174.30,147.36],[1170.63,145.93],[1169.52,142.12],[1168.81,138.18],[1168.10,134.24],[1167.37,130.30],[1166.61,126.37],[1165.91,122.43],[1165.20,118.49],[1164.50,114.55],[1164.03,110.58],[1163.74,106.59],[1164.60,103.04],[1168.49,102.53],[1172.50,102.53],[1176.50,102.53],[1180.51,102.53],[1184.51,102.53],[1188.52,102.53],[1192.52,102.53],[1196.52,102.53],[1200.53,102.53],[1204.53,102.53],[1208.54,102.53],[1212.54,102.53],[1216.55,102.53],[1220.55,102.53],[1224.52,102.18],[1226.27,99.11],[1225.90,95.13],[1225.39,91.17],[1224.65,87.23],[1223.93,83.29],[1223.22,79.35],[1222.57,75.40],[1221.84,71.47],[1220.86,67.59],[1218.20,64.70],[1214.98,62.31],[1211.51,60.31],[1207.96,58.48],[1204.29,56.86],[1200.60,55.31],[1196.85,53.93],[1193.06,52.63],[1189.19,51.58],[1185.27,50.80],[1181.35,49.99],[1177.40,49.33],[1173.42,49.02],[1169.45,48.61],[1165.44,48.61],[1161.44,48.61],[1157.46,48.96],[1153.46,49.09],[1149.51,49.71],[1145.59,50.50],[1141.68,51.36],[1137.89,52.64],[1134.17,54.13],[1130.52,55.76],[1127.06,57.76],[1123.73,59.99],[1120.69,62.59],[1117.78,65.32],[1115.17,68.36],[1112.91,71.67],[1110.85,75.10],[1108.98,78.64],[1107.41,82.32],[1106.23,86.14],[1105.17,90.00],[1104.20,93.88],[1103.72,97.85],[1103.11,101.80],[1102.94,105.80],[1102.83,109.79],[1102.91,113.76],[1102.94,117.76],[1103.19,121.75],[1103.76,125.70],[1104.29,129.67],[1104.91,133.62],[1105.87,137.51],[1107.03,141.34]],
    [[60.87,135.62],[59.74,131.79],[58.83,127.90],[58.21,123.96],[57.68,120.00],[57.19,116.04],[57.18,112.05],[56.87,108.08],[57.19,104.12],[57.50,100.15],[58.04,96.20],[58.82,92.29],[59.93,88.46],[61.18,84.67],[62.75,81.00],[64.69,77.51],[66.90,74.18],[69.24,70.94],[71.81,67.90],[74.65,65.08],[77.76,62.60],[81.05,60.32],[84.43,58.20],[88.01,56.43],[91.70,54.90],[95.43,53.48],[99.31,52.52],[103.21,51.66],[107.13,50.93],[111.11,50.65],[115.07,50.25],[119.07,50.25],[123.05,50.35],[127.03,50.66],[130.99,51.10],[134.89,51.93],[138.81,52.68],[142.69,53.62],[146.53,54.72],[150.25,56.18],[153.96,57.66],[157.63,59.23],[161.25,60.92],[164.80,62.75],[168.20,64.84],[171.55,67.02],[174.89,69.21],[178.39,71.09],[182.28,71.87],[185.78,70.07],[188.32,67.00],[190.67,63.77],[193.06,60.57],[195.45,57.36],[197.82,54.15],[200.20,50.94],[202.57,47.73],[204.91,44.49],[207.13,41.17],[208.62,37.51],[207.99,33.73],[205.37,30.74],[202.18,28.34],[198.92,26.03],[195.57,23.86],[192.17,21.75],[188.78,19.64],[185.25,17.77],[181.68,15.99],[178.10,14.21],[174.46,12.58],[170.75,11.10],[167.04,9.62],[163.32,8.14],[159.50,7.00],[155.67,5.88],[151.78,4.95],[147.87,4.13],[143.96,3.30],[140.05,2.52],[136.11,1.89],[132.14,1.43],[128.18,1.03],[124.21,0.75],[120.24,0.41],[116.27,0.03],[112.28,0.00],[108.28,0.00],[104.30,0.16],[100.33,0.49],[96.36,0.82],[92.39,1.21],[88.43,1.71],[84.50,2.38],[80.59,3.20],[76.69,4.06],[72.79,4.94],[68.95,6.03],[65.15,7.28],[61.44,8.76],[57.74,10.26],[54.15,12.02],[50.58,13.80],[47.05,15.67],[43.63,17.73],[40.30,19.94],[37.07,22.29],[34.01,24.86],[31.00,27.48],[28.14,30.27],[25.40,33.18],[22.77,36.18],[20.34,39.35],[17.94,42.54],[15.74,45.87],[13.71,49.31],[11.85,52.85],[10.09,56.43],[8.48,60.08],[7.15,63.85],[5.88,67.64],[4.65,71.44],[3.48,75.25],[2.60,79.15],[2.03,83.10],[1.34,87.03],[0.81,90.98],[0.42,94.94],[0.07,98.91],[0.00,102.90],[0.00,106.90],[0.00,110.89],[0.03,114.88],[0.41,118.85],[0.91,122.81],[1.55,126.75],[2.12,130.70],[2.82,134.63],[3.53,138.56],[4.48,142.44],[5.58,146.28],[6.75,150.09],[8.02,153.88],[9.27,157.68],[10.60,161.44],[12.20,165.10],[13.83,168.75],[15.60,172.33],[17.76,175.64],[21.46,177.01],[25.44,177.29],[29.43,177.29],[33.43,177.29],[37.42,177.29],[41.42,177.29],[45.41,177.29],[49.41,177.29],[53.40,177.29],[57.40,177.29],[61.39,177.29],[65.39,177.29],[69.38,177.29],[73.38,177.29],[77.37,177.29],[81.36,177.29],[85.36,177.29],[89.35,177.29],[93.35,177.29],[97.34,177.29],[101.34,177.29],[105.33,177.29],[109.33,177.29],[113.32,177.29],[117.23,178.01],[120.72,179.86],[123.79,182.41],[127.06,184.71],[130.35,186.97],[133.70,189.16],[137.15,191.16],[140.70,192.99],[144.33,194.66],[148.05,196.11],[151.85,197.32],[155.65,198.55],[159.55,199.41],[163.49,200.08],[167.44,200.59],[171.40,200.98],[175.39,201.02],[179.35,201.01],[183.35,200.98],[187.31,200.62],[191.26,200.04],[195.21,199.49],[199.06,198.43],[202.90,197.34],[206.67,196.02],[210.31,194.39],[213.84,192.51],[217.19,190.34],[220.50,188.10],[223.74,185.77],[226.96,183.44],[230.81,182.56],[234.60,183.75],[237.63,186.35],[240.55,189.07],[243.54,191.71],[246.43,194.47],[249.41,197.13],[252.34,199.84],[255.26,202.56],[258.25,205.21],[261.15,207.96],[263.66,210.98],[264.33,214.83],[262.72,218.45],[259.92,221.29],[256.90,223.91],[253.82,226.45],[250.69,228.93],[247.46,231.28],[244.09,233.42],[240.68,235.50],[237.22,237.50],[233.65,239.29],[230.00,240.91],[226.36,242.54],[222.60,243.89],[218.82,245.20],[214.97,246.24],[211.10,247.23],[207.22,248.18],[203.29,248.88],[199.34,249.43],[195.39,249.96],[191.43,250.45],[187.46,250.82],[183.47,250.82],[179.47,250.82],[175.48,250.82],[171.48,250.82],[167.52,250.41],[163.55,250.01],[159.60,249.46],[155.64,248.92],[151.68,248.37],[147.76,247.66],[143.86,246.80],[139.99,245.81],[136.16,244.66],[132.35,243.48],[128.52,242.34],[124.74,241.04],[121.02,239.59],[117.35,238.01],[113.69,236.40],[110.12,234.62],[106.62,232.71]],
    [[322.30,152.64],[326.30,152.78],[330.30,152.78],[334.31,152.78],[338.31,152.78],[342.31,152.78],[346.32,152.78],[350.32,152.78],[354.33,152.78],[358.33,152.78],[362.33,152.78],[366.34,152.78],[370.34,152.78],[374.35,152.78],[378.35,152.78],[382.35,152.78],[386.36,152.78],[390.36,152.78],[394.36,152.78],[398.37,152.78],[402.37,152.78],[406.38,152.78],[410.38,152.78],[414.38,152.78],[418.36,153.07],[421.00,155.76],[421.80,159.68],[422.45,163.63],[423.19,167.56],[423.85,171.51],[424.85,175.34],[428.33,177.01],[432.31,177.29],[436.32,177.29],[440.32,177.29],[444.32,177.29],[448.33,177.29],[452.33,177.29],[456.34,177.29],[460.34,177.29],[464.34,177.29],[468.35,177.29],[472.35,177.29],[476.35,177.29],[480.36,177.29],[484.36,177.29],[488.37,177.29],[492.37,177.29],[496.37,177.29],[500.38,177.29],[504.38,177.29],[508.39,177.29],[512.34,177.68],[514.63,180.64],[515.35,184.58],[515.99,188.53],[516.72,192.47],[517.45,196.41],[518.09,200.36],[518.81,204.29],[519.51,208.24],[520.21,212.18],[520.92,216.12],[521.58,220.06],[522.31,224.00],[522.96,227.95],[523.69,231.88],[524.41,235.82],[524.60,239.82],[524.76,243.78],[521.46,245.46],[517.46,245.51],[513.45,245.51],[509.45,245.51],[505.45,245.51],[501.44,245.51],[497.44,245.51],[493.44,245.51],[489.43,245.51],[485.43,245.51],[481.42,245.51],[477.42,245.51],[473.42,245.43],[469.58,244.49],[468.11,240.90],[467.37,236.96],[466.70,233.02],[465.99,229.08],[465.29,225.14],[464.60,221.19],[463.95,217.24],[463.22,213.31],[462.54,209.36],[461.60,205.47]],
    [[646.65,171.57],[649.43,168.74],[651.08,165.18],[652.26,161.38],[653.49,157.61],[654.64,153.81],[655.85,150.03],[657.05,146.25],[658.28,142.47],[659.43,138.67],[660.64,134.89],[661.87,131.12],[663.04,127.33],[664.26,123.55],[665.42,119.75],[666.67,115.98],[667.80,112.18],[668.99,108.39],[669.50,104.46],[669.88,100.53],[667.14,98.45],[663.17,98.45],[659.20,98.45],[655.23,98.45],[651.26,98.45],[647.29,98.45],[643.32,98.45],[639.35,98.45],[635.38,98.45],[631.41,98.45],[627.44,98.45],[623.47,98.45],[619.50,98.45],[615.53,98.45],[611.56,98.45],[607.59,98.45],[603.62,98.45],[600.66,100.13],[601.40,104.00],[602.40,107.84]],
    [[658.09,244.42],[661.96,245.38],[665.95,245.51],[669.94,245.51],[673.94,245.51],[677.94,245.51],[681.93,245.51],[685.93,245.51],[689.93,245.51],[693.92,245.51],[697.92,245.51],[701.92,245.51],[705.91,245.51],[709.91,245.51],[713.90,245.43],[717.72,244.35],[719.34,240.79],[720.37,236.93],[721.40,233.07],[722.42,229.20],[723.46,225.34],[724.50,221.48],[725.57,217.64],[726.64,213.79],[727.71,209.94],[728.77,206.09],[729.76,202.21],[730.78,198.35],[731.84,194.50],[732.90,190.65],[733.95,186.79],[734.45,182.83],[734.76,178.88],[731.65,177.29],[727.66,177.29],[723.66,177.29],[719.66,177.29],[715.67,177.29],[711.67,177.29],[707.67,177.29],[703.68,177.29],[699.68,177.29],[695.68,177.29],[691.69,177.29],[687.69,177.29],[683.69,177.29],[679.70,177.29],[675.70,177.29],[671.70,177.29],[667.70,177.29],[663.71,177.29],[659.71,177.29],[655.71,177.29],[651.72,177.29],[647.96,176.15],[644.34,175.98],[640.73,177.29],[636.73,177.29],[632.74,177.29],[628.74,177.29],[624.74,177.29],[620.74,177.29],[616.75,177.29],[612.75,177.29],[608.75,177.29],[604.76,177.29],[600.76,177.29],[596.76,177.29],[592.77,177.29],[588.77,177.26],[584.88,176.41],[582.59,173.21],[580.45,169.84],[578.30,166.46],[576.16,163.09],[574.02,159.72],[571.87,156.35],[569.73,152.97],[567.59,149.60],[565.44,146.23],[563.30,142.85],[561.17,139.47],[559.04,136.09],[556.90,132.71],[554.77,129.33],[552.64,125.95],[550.50,122.57],[548.37,119.19],[546.23,115.81],[544.10,112.43],[541.97,109.05],[539.84,105.67],[537.71,102.29],[535.58,98.91],[533.45,95.52],[531.32,92.14],[529.19,88.76],[527.06,85.38],[524.93,82.00],[522.80,78.61],[520.68,75.23],[518.56,71.84],[516.43,68.46],[514.31,65.07],[512.19,61.68],[510.06,58.30],[507.94,54.91],[505.82,51.53],[503.69,48.14],[501.57,44.75],[499.46,41.36],[497.35,37.97],[495.23,34.58],[493.12,31.18],[491.01,27.79],[488.89,24.40],[486.78,21.01],[484.67,17.61],[482.66,14.17],[481.61,10.32],[481.05,6.41],[484.86,5.72],[488.85,5.72],[492.85,5.72],[496.85,5.72],[500.84,5.72],[504.84,5.72],[508.84,5.72],[512.83,5.72],[516.83,5.72],[520.83,5.72],[524.82,5.72],[528.82,5.72],[532.82,5.72],[536.81,5.72],[540.72,6.37],[543.58,9.11],[545.75,12.47],[547.78,15.91],[549.81,19.35],[551.85,22.79],[553.88,26.23],[555.92,29.67],[557.96,33.10],[559.98,36.55],[562.03,39.98],[564.09,43.41],[566.43,46.65],[570.00,48.17],[573.96,48.61],[577.95,48.61],[581.95,48.61],[585.95,48.61],[589.94,48.61],[593.94,48.61],[597.94,48.61],[601.93,48.61],[605.93,48.61],[609.93,48.61],[613.92,48.61],[617.92,48.61],[621.92,48.61],[625.91,48.61],[629.91,48.61],[633.91,48.61],[637.90,48.61],[641.90,48.61],[645.90,48.61],[649.89,48.61],[653.89,48.61],[657.89,48.61],[661.89,48.61],[665.88,48.61],[669.88,48.61],[673.88,48.61],[677.87,48.61],[681.81,47.98],[684.49,45.31],[685.48,41.44],[686.44,37.56],[687.39,33.68],[688.38,29.80],[689.36,25.93],[690.29,22.04],[691.28,18.17],[692.27,14.30],[693.18,10.41],[694.82,6.88],[698.55,5.72],[702.54,5.72],[706.54,5.72],[710.54,5.72],[714.53,5.72],[718.53,5.72],[722.53,5.72],[726.52,5.72],[730.52,5.72],[734.52,5.72],[738.51,5.72],[742.51,5.72],[746.51,5.72],[749.91,7.04],[749.61,11.01],[749.09,14.97],[748.10,18.84],[747.03,22.69],[745.96,26.54],[744.90,30.39],[743.93,34.26],[742.88,38.12],[741.82,41.97],[740.78,45.83],[739.74,49.69],[738.69,53.55],[737.63,57.40],[736.56,61.25],[735.51,65.10],[734.48,68.96],[733.46,72.83],[732.43,76.69],[731.37,80.54],[730.30,84.39],[729.23,88.24],[728.24,92.11],[727.17,95.96],[726.10,99.81],[725.03,103.66],[724.00,107.52],[722.97,111.38],[721.95,115.25],[720.90,119.10],[719.83,122.95],[718.76,126.80],[717.72,130.66],[716.68,134.52],[715.64,138.38],[714.59,142.23],[713.54,146.09],[712.42,149.92]],
    [[476.58,146.24],[475.75,142.34],[475.07,138.40],[474.36,134.47],[473.66,130.54],[472.98,126.60],[472.25,122.67],[471.62,118.73],[470.92,114.79],[470.21,110.86],[469.51,106.93],[468.86,102.99],[468.13,99.06],[467.47,95.12],[466.77,91.19],[466.08,87.25],[465.36,83.32],[464.73,79.37],[464.03,75.44],[463.32,71.51],[462.62,67.58],[461.91,63.64],[461.25,59.70],[460.58,55.77],[459.88,51.83],[459.17,47.90],[458.48,43.97],[457.76,40.04],[457.12,36.09],[456.39,32.17],[455.73,28.22],[455.02,24.29],[454.35,20.35],[453.62,16.43],[452.97,12.48],[452.17,8.57],[449.55,5.93],[445.57,5.72],[441.58,5.72],[437.58,5.72],[433.58,5.72],[429.59,5.72],[425.59,5.72],[421.60,5.72],[417.60,5.72],[413.60,5.72],[409.61,5.72],[405.61,5.72],[401.61,5.72],[397.63,5.90],[396.14,9.08],[396.32,13.07],[396.81,17.03],[397.53,20.95],[398.19,24.90],[398.90,28.83],[399.57,32.77],[400.30,36.69],[400.94,40.64],[401.64,44.57],[402.33,48.50],[402.98,52.45],[403.71,56.38],[404.37,60.32],[405.09,64.25],[405.75,68.19],[406.48,72.11],[407.12,76.06],[407.83,79.99],[408.52,83.92],[409.16,87.87],[409.87,91.80],[410.15,95.78],[410.50,99.74],[407.65,101.89],[403.67,102.12],[399.67,102.12],[395.68,102.12],[391.68,102.12],[387.68,102.12],[383.69,102.12],[379.69,102.12],[375.70,102.12],[371.70,102.12],[367.70,102.12],[363.71,102.12],[359.71,102.12],[355.71,102.12],[351.72,102.12],[347.72,102.12],[343.73,102.12],[339.73,102.12],[335.73,102.12],[331.74,102.12],[327.74,102.12],[323.75,102.12],[319.75,102.12],[315.76,102.02],[311.89,101.13],[310.10,97.78],[309.45,93.83],[308.72,89.91],[308.06,85.96],[307.34,82.04],[306.68,78.10],[306.01,74.16],[305.30,70.22],[304.65,66.28],[303.92,62.36],[303.27,58.41],[302.54,54.48],[301.88,50.54],[301.15,46.62],[300.51,42.67],[299.82,38.74],[299.12,34.80],[298.47,30.86],[297.73,26.94],[297.08,22.99],[296.38,19.06],[295.70,15.12],[294.97,11.20],[293.98,7.35],[290.53,5.75],[286.54,5.72],[282.54,5.72],[278.54,5.72],[274.55,5.72],[270.55,5.72],[266.56,5.72],[262.56,5.72],[258.56,5.72],[254.57,5.72],[250.57,5.72],[246.57,5.72],[242.58,5.72],[238.69,6.27],[238.15,10.08],[238.46,14.05],[238.98,18.00],[239.68,21.94],[240.31,25.88],[241.04,29.81],[241.72,33.75],[242.42,37.68],[243.13,41.61],[243.81,45.55],[244.53,49.48],[245.16,53.42],[245.87,57.36],[246.57,61.29],[247.28,65.22],[247.92,69.16],[248.65,73.09],[249.31,77.03],[250.03,80.96],[250.69,84.90],[251.42,88.83],[252.07,92.77],[252.80,96.70],[253.46,100.64],[254.18,104.57],[254.87,108.51],[255.56,112.44],[256.22,116.38],[256.95,120.31],[257.61,124.25],[258.33,128.18],[259.02,132.11],[259.71,136.05],[260.43,139.98],[261.10,143.92],[261.76,147.86],[262.47,151.79],[263.17,155.72],[263.86,159.66],[264.58,163.59],[265.23,167.53],[265.97,171.46],[266.83,175.35],[270.29,176.97],[274.26,177.29],[278.26,177.29],[282.25,177.29],[286.25,177.29],[290.25,177.29],[294.24,177.29],[298.24,177.29],[302.24,177.29],[306.23,177.29],[310.23,177.29],[314.22,177.29],[318.22,177.29],[322.22,177.29],[326.21,177.29],[330.21,177.29],[334.21,177.29],[338.20,177.29],[342.20,177.29],[346.19,177.29],[350.19,177.29],[354.11,177.81],[356.20,180.94],[356.91,184.87],[357.61,188.81],[358.32,192.74],[359.02,196.67],[359.73,200.60],[360.36,204.55],[361.08,208.48],[361.76,212.41],[362.47,216.35],[363.17,220.28],[363.88,224.21],[364.58,228.14],[365.29,232.08],[365.93,236.02],[366.21,240.00],[366.27,243.97],[362.78,245.46],[358.78,245.51],[354.79,245.51],[350.79,245.51],[346.80,245.51],[342.80,245.51],[338.80,245.51],[334.81,245.51],[330.81,245.51],[326.81,245.51],[322.82,245.51],[318.82,245.51],[314.83,245.42],[311.03,244.41],[309.60,240.82],[308.90,236.89],[308.20,232.95],[307.49,229.02],[306.83,225.08],[306.10,221.15],[305.45,217.21],[304.75,213.28],[304.07,209.34],[303.10,205.47]],
    [[989.79,5.72],[985.78,5.72],[981.78,5.72],[977.77,5.72],[973.77,5.72],[969.76,5.72],[965.76,5.72],[961.75,5.72],[957.75,5.72],[953.74,5.72],[949.74,5.72],[945.73,5.72],[941.72,5.72],[937.72,5.72],[933.72,5.80],[930.03,7.19],[927.73,10.45],[925.65,13.88],[923.58,17.30],[921.50,20.73],[919.42,24.15],[917.35,27.58],[915.28,31.01],[913.21,34.44],[911.14,37.87],[909.06,41.29],[906.98,44.71],[904.90,48.13],[902.82,51.56],[900.73,54.97],[898.63,58.39],[896.54,61.80],[894.45,65.22],[892.35,68.63],[890.25,72.04],[888.14,75.45],[886.04,78.86],[883.80,82.17],[879.98,83.22],[875.99,83.33],[871.98,83.33],[867.98,83.33],[863.97,83.33],[859.97,83.33],[855.96,83.33],[851.96,83.33],[847.99,82.83],[845.41,80.17],[844.66,76.24],[843.96,72.29],[843.25,68.35],[842.62,64.40],[841.91,60.46],[841.21,56.52],[840.50,52.58],[839.79,48.64],[839.12,44.69],[838.39,40.75],[837.75,36.80],[837.02,32.86],[836.34,28.91],[835.63,24.97],[834.93,21.03],[834.25,17.08],[833.52,13.15],[832.87,9.20],[830.55,6.18],[826.60,5.72],[822.60,5.72],[818.59,5.72],[814.59,5.72],[810.58,5.72],[806.58,5.72],[802.57,5.72],[798.57,5.72],[794.56,5.72],[790.56,5.72],[786.55,5.72],[782.55,5.72],[778.55,5.79],[776.55,8.61],[776.78,12.60],[777.23,16.57],[777.96,20.51],[778.61,24.46],[779.35,28.39],[780.00,32.34],[780.73,36.28],[781.38,40.23],[782.12,44.17],[782.77,48.12],[783.50,52.06],[784.16,56.01],[784.88,59.94],[785.57,63.89],[786.27,67.83],[786.93,71.78],[787.66,75.72],[788.32,79.67],[789.03,83.61],[789.73,87.55],[790.43,91.49],[791.14,95.43],[791.79,99.38],[792.48,103.33],[793.19,107.27],[793.89,111.21],[794.57,115.16],[795.30,119.09],[795.93,123.05],[796.64,126.99],[797.35,130.93],[798.05,134.87],[798.68,138.83],[799.41,142.76],[800.09,146.71],[800.80,150.65],[801.51,154.59],[802.19,158.54],[802.84,162.49],[803.55,166.43],[804.25,170.37],[805.04,174.29],[807.90,176.78],[811.86,177.29],[815.87,177.29],[819.87,177.29],[823.88,177.29],[827.88,177.29],[831.89,177.29],[835.89,177.29],[839.90,177.29],[843.90,177.29],[847.91,177.29],[851.91,177.29],[855.92,177.29],[859.92,177.29],[863.93,177.29],[867.93,177.29],[871.94,177.29],[875.95,177.29],[879.95,177.29],[883.96,177.29],[887.96,177.29],[891.89,177.86],[894.02,180.98],[894.70,184.92],[895.44,188.86],[896.08,192.81],[897.63,196.38],[901.39,197.51],[905.38,197.71],[909.38,197.71],[913.39,197.71],[917.39,197.71],[921.40,197.71],[925.40,197.71],[929.41,197.71],[933.41,197.71],[937.42,197.71],[941.42,197.71],[945.43,197.71],[949.44,197.71],[953.43,197.58]],
    [[990.88,6.94],[989.88,10.80],[988.90,14.64],[986.79,18.02],[984.66,21.39],[982.53,24.77],[980.41,28.14],[978.27,31.50],[976.13,34.86],[973.99,38.23],[971.85,41.59],[969.72,44.96],[967.60,48.34],[965.47,51.71],[963.35,55.08],[961.22,58.45],[959.10,61.83],[956.97,65.20],[954.84,68.57],[952.72,71.94],[950.59,75.31],[948.47,78.69],[946.50,82.12],[945.55,85.99],[946.68,89.56],[950.29,91.15],[953.99,92.65],[957.68,94.14],[961.26,95.90],[964.88,97.56],[968.30,99.61],[971.71,101.66],[975.10,103.77],[978.32,106.11],[981.40,108.65],[984.35,111.31],[987.27,114.02],[989.92,117.00],[992.48,120.06],[994.79,123.30],[996.97,126.64],[999.09,130.01],[1001.03,133.49],[1002.69,137.12],[1004.24,140.79],[1005.65,144.51],[1006.94,148.28]],
    [[857.84,154.41],[857.14,150.47],[856.43,146.52],[855.72,142.58],[855.29,138.60],[854.96,134.62],[855.19,130.76],[858.94,129.90],[862.95,129.90],[866.96,129.90],[870.97,129.90],[874.97,129.90],[878.98,129.90],[882.99,129.90],[887.00,129.90],[891.01,129.90],[895.02,129.90],[899.03,129.90],[903.04,129.90],[907.05,129.90],[911.05,129.90],[915.06,129.90],[919.04,130.30],[922.99,130.96],[926.91,131.74],[930.65,133.17],[934.33,134.75],[937.78,136.79],[941.03,139.14],[943.86,141.95],[946.57,144.90],[948.77,148.25],[950.74,151.74],[952.24,155.45],[953.47,159.27],[954.29,163.19],[954.70,167.16],[955.07,171.14],[954.93,175.13],[958.04,177.07],[962.04,177.29],[966.05,177.29],[970.05,177.29],[974.06,177.29],[978.07,177.29],[982.08,177.29],[986.09,177.29],[990.10,177.29],[994.11,177.29],[998.12,177.29],[1002.12,177.29],[1006.13,177.29],[1010.14,177.29],[1014.15,177.29],[1018.16,177.29],[1022.17,177.29],[1026.18,177.29],[1030.19,177.29],[1034.20,177.29],[1038.20,177.30],[1041.39,179.32],[1041.31,183.25],[1041.00,187.24],[1040.19,191.16],[1039.38,195.08],[1038.24,198.92],[1036.75,202.65],[1035.20,206.34],[1033.42,209.92],[1031.40,213.39],[1029.15,216.70],[1026.68,219.86],[1023.95,222.79],[1021.11,225.62],[1018.15,228.32],[1014.95,230.73],[1011.60,232.93],[1008.12,234.91],[1004.58,236.80],[1001.00,238.60],[997.25,240.02],[993.43,241.23],[989.58,242.33],[985.71,243.36],[981.75,243.93],[977.80,244.56],[973.83,245.07],[969.82,245.11],[965.84,245.50],[961.84,245.51],[957.83,245.51],[953.82,245.51],[949.81,245.51],[945.80,245.51],[941.79,245.51],[937.78,245.51],[933.77,245.51],[929.77,245.51],[925.76,245.51],[921.75,245.51],[917.74,245.51],[913.73,245.51],[909.72,245.51],[905.71,245.51],[901.70,245.51],[897.70,245.51],[893.69,245.51],[889.68,245.51],[885.67,245.51],[881.66,245.51],[877.65,245.51],[873.64,245.51],[869.63,245.51],[865.62,245.51],[861.62,245.51],[857.61,245.51],[853.60,245.51],[849.59,245.51],[845.58,245.51],[841.57,245.51],[837.56,245.51],[833.55,245.51],[829.55,245.51],[825.55,245.34],[823.35,242.67],[823.75,238.69],[824.14,234.71],[824.98,230.79],[825.81,226.87],[826.71,222.97],[827.56,219.05],[828.43,215.14],[829.31,211.22],[830.15,207.31],[831.15,203.43]]
];
WORD_closed = [0, 0, 0, 0, 0, 0, 0, 0, 0, 0];
WORD_pixels = [[1368.46,216.09],[1371.47,232.75],[1378.87,245.48],[1395.79,245.51],[1412.72,245.51],[1429.65,245.51],[1446.58,245.51],[1463.51,245.51],[1480.44,245.51],[1497.37,245.51],[1514.30,245.51],[1531.22,245.51],[1548.15,245.51],[1555.64,235.69],[1552.63,219.04],[1549.51,202.41],[1534.81,198.53],[1517.88,198.53],[1500.95,198.53],[1484.02,198.53],[1467.09,198.53],[1450.17,198.53],[1433.24,198.53],[1420.25,192.34],[1414.81,177.43],[1397.89,177.29],[1380.96,177.29],[1364.03,177.29],[1347.10,177.29],[1330.52,175.77],[1327.12,159.30],[1324.20,142.63],[1321.27,125.96],[1318.27,109.30],[1315.36,92.63],[1312.46,75.96],[1309.55,59.28],[1306.64,42.61],[1303.66,25.95],[1301.45,9.21],[1315.68,5.72],[1332.61,5.72],[1349.54,5.72],[1366.47,5.72],[1383.40,5.72],[1400.33,5.72],[1417.26,5.72],[1434.19,5.72],[1451.12,5.72],[1468.04,5.72],[1484.95,5.98],[1489.81,21.46],[1492.83,38.11],[1491.20,52.91],[1474.28,53.10],[1457.35,53.10],[1440.42,53.10],[1423.50,53.10],[1406.57,53.10],[1389.64,53.10],[1372.71,53.10],[1366.50,63.97],[1369.35,80.66],[1372.17,97.34],[1384.29,104.58],[1401.22,104.58],[1418.15,104.58],[1435.08,104.58],[1452.00,104.58],[1468.93,104.58],[1485.86,104.58],[1495.84,114.14],[1498.87,130.79],[1501.22,147.51],[1485.56,149.92],[1468.63,149.92],[1451.70,149.92],[1434.77,149.92],[1417.84,149.92],[1400.92,149.92],[1383.99,149.92],[1144.61,230.66],[1159.74,238.38],[1175.74,244.09],[1192.22,248.26],[1209.05,250.51],[1226.00,251.23],[1242.94,250.27],[1259.68,247.45],[1275.96,242.55],[1291.32,235.33],[1305.45,225.88],[1316.00,213.16],[1304.66,201.05],[1291.54,190.23],[1276.99,183.67],[1262.94,193.19],[1247.15,199.37],[1230.41,202.21],[1213.45,201.60],[1196.80,198.40],[1180.96,192.34],[1166.63,183.23],[1151.41,177.29],[1134.40,177.29],[1117.39,177.29],[1100.39,177.29],[1083.38,177.29],[1066.40,176.92],[1057.69,163.42],[1052.69,147.18],[1049.54,130.48],[1047.79,113.61],[1047.79,96.66],[1049.52,79.78],[1053.89,63.36],[1060.97,47.95],[1070.61,33.98],[1082.91,22.28],[1097.23,13.15],[1112.87,6.49],[1129.40,2.55],[1146.24,0.50],[1163.20,0.12],[1180.09,1.61],[1196.81,4.60],[1213.23,8.96],[1229.03,15.26],[1243.92,23.42],[1257.82,33.20],[1265.64,47.45],[1268.49,64.21],[1271.42,80.96],[1274.36,97.70],[1277.22,114.46],[1280.14,131.21],[1280.06,147.12],[1263.09,147.47],[1246.08,147.47],[1229.07,147.47],[1212.06,147.47],[1195.06,147.47],[1178.05,147.47],[1168.57,136.97],[1165.51,120.24],[1164.00,103.51],[1180.70,102.53],[1197.71,102.53],[1214.72,102.53],[1225.90,95.97],[1223.19,79.21],[1217.31,63.99],[1202.34,56.02],[1186.14,50.99],[1169.35,48.61],[1152.39,49.26],[1135.97,53.43],[1121.40,61.98],[1110.83,75.14],[1104.86,90.99],[1102.94,107.82],[1103.62,124.73],[1107.03,141.34],[60.87,135.62],[57.51,119.03],[57.20,102.15],[60.82,85.65],[69.20,71.00],[81.81,59.81],[97.25,52.94],[113.97,50.36],[130.86,51.10],[147.33,55.01],[162.89,61.74],[177.30,70.67],[190.56,63.93],[200.67,50.31],[208.78,35.77],[196.61,24.53],[181.91,16.11],[166.37,9.36],[150.11,4.61],[133.44,1.60],[116.60,0.05],[99.68,0.58],[82.89,2.70],[66.46,6.84],[50.93,13.63],[36.61,22.66],[24.35,34.34],[14.45,48.07],[7.29,63.41],[2.51,79.67],[0.41,96.45],[0.00,113.38],[2.02,130.18],[5.70,146.72],[11.18,162.76],[19.93,176.66],[36.83,177.29],[53.79,177.29],[70.76,177.29],[87.72,177.29],[104.68,177.29],[120.97,180.08],[134.82,189.83],[150.22,196.85],[166.72,200.53],[183.61,200.98],[200.26,198.12],[215.72,191.32],[230.03,182.58],[243.69,191.84],[256.12,203.37],[263.63,216.87],[251.36,228.41],[237.10,237.56],[221.54,244.25],[205.17,248.62],[188.38,250.82],[171.42,250.82],[154.60,248.78],[138.05,245.21],[121.93,239.97],[106.62,232.71],[322.30,152.64],[339.22,152.78],[356.15,152.78],[373.07,152.78],[390.00,152.78],[406.92,152.78],[421.31,157.18],[424.32,173.83],[439.59,177.29],[456.52,177.29],[473.44,177.29],[490.37,177.29],[507.29,177.29],[515.95,188.35],[518.94,205.01],[521.87,221.67],[524.51,238.36],[514.00,245.51],[497.08,245.51],[480.15,245.51],[467.69,238.75],[464.73,222.09],[461.60,205.47],[646.65,171.57],[653.90,156.35],[659.07,139.95],[664.26,123.55],[669.14,107.08],[660.53,98.45],[643.32,98.45],[626.12,98.45],[608.91,98.45],[602.40,107.84],[658.09,244.42],[674.94,245.51],[691.92,245.51],[708.91,245.51],[720.37,236.93],[724.80,220.53],[729.27,204.15],[733.68,187.75],[727.66,177.29],[710.67,177.29],[693.68,177.29],[676.70,177.29],[659.71,177.29],[643.55,176.59],[626.74,177.29],[609.75,177.29],[592.77,177.29],[579.91,168.99],[570.80,154.66],[561.70,140.32],[552.64,125.95],[543.57,111.59],[534.52,97.22],[525.47,82.84],[516.43,68.46],[507.41,54.07],[498.40,39.66],[489.42,25.25],[481.61,10.32],[493.85,5.72],[510.83,5.72],[527.82,5.72],[543.58,9.11],[552.36,23.65],[561.01,38.27],[572.96,48.59],[589.94,48.61],[606.93,48.61],[623.92,48.61],[640.90,48.61],[657.89,48.61],[674.87,48.61],[685.97,39.50],[690.05,23.01],[694.82,6.88],[711.53,5.72],[728.52,5.72],[745.51,5.72],[748.10,18.84],[743.67,35.23],[739.20,51.61],[734.76,68.00],[730.30,84.39],[725.85,100.78],[721.40,117.17],[716.95,133.55],[712.42,149.92],[476.58,146.24],[473.49,129.57],[470.58,112.86],[467.68,96.15],[464.74,79.44],[461.73,62.75],[458.80,46.05],[455.89,29.33],[452.99,12.62],[440.74,5.72],[423.77,5.72],[406.80,5.72],[396.28,12.86],[399.03,29.59],[401.93,46.30],[404.84,63.01],[407.77,79.71],[410.21,96.48],[397.99,102.12],[381.02,102.12],[364.06,102.12],[347.09,102.12],[330.12,102.12],[313.20,101.58],[308.13,86.38],[305.22,69.67],[302.31,52.96],[299.41,36.25],[296.47,19.54],[290.04,5.73],[273.08,5.72],[256.11,5.72],[239.20,6.06],[239.76,22.35],[242.67,39.06],[245.57,55.77],[248.56,72.47],[251.48,89.18],[254.41,105.88],[257.36,122.59],[260.29,139.29],[263.23,156.00],[266.16,172.70],[280.50,177.29],[297.47,177.29],[314.43,177.29],[331.40,177.29],[348.37,177.29],[357.45,187.98],[360.38,204.69],[363.39,221.38],[366.01,238.12],[355.70,245.51],[338.73,245.51],[321.77,245.51],[309.23,238.82],[306.27,222.12],[303.10,205.47],[989.79,5.72],[972.61,5.72],[955.43,5.72],[938.25,5.72],[925.33,14.42],[916.43,29.12],[907.52,43.81],[898.58,58.48],[889.58,73.11],[877.57,83.33],[860.39,83.33],[845.23,79.45],[842.25,62.54],[839.28,45.62],[836.30,28.71],[833.32,11.79],[820.07,5.72],[802.89,5.72],[785.71,5.72],[776.96,14.59],[779.88,31.51],[782.81,48.43],[785.83,65.34],[788.78,82.26],[791.75,99.18],[794.72,116.09],[797.68,133.01],[800.67,149.92],[803.63,166.84],[813.44,177.29],[830.62,177.29],[847.80,177.29],[864.98,177.29],[882.16,177.29],[894.61,184.30],[901.91,197.61],[919.08,197.71],[936.26,197.71],[953.43,197.58],[990.88,6.94],[984.27,22.01],[975.35,36.09],[966.44,50.18],[957.55,64.28],[948.66,78.38],[950.63,91.28],[965.82,98.10],[979.74,107.24],[991.54,118.96],[1000.72,132.83],[1006.94,148.28],[857.84,154.41],[855.19,137.86],[864.45,129.90],[881.24,129.90],[898.03,129.90],[914.81,129.90],[931.12,133.35],[944.73,142.85],[952.91,157.34],[954.85,173.88],[969.55,177.29],[986.34,177.29],[1003.13,177.29],[1019.91,177.29],[1036.70,177.29],[1040.36,190.43],[1035.20,206.34],[1026.20,220.44],[1013.72,231.59],[998.89,239.40],[982.75,243.87],[966.10,245.50],[949.31,245.51],[932.52,245.51],[915.73,245.51],[898.95,245.51],[882.16,245.51],[865.37,245.51],[848.59,245.51],[831.80,245.51],[823.96,236.20],[827.39,219.78],[831.15,203.43]];
WORD_bbox = [1556.37, 251.23];
