booherbg/tedxfargo-charge-sign/src/parts/word_layout.scad

// AUTO-GENERATED by tools/gen_pieces.py from src/parts/word_cuts.json — do not hand-edit
wl_face = [-17.00,-21.89,1580.25,273.12];
wl_paths = [
  [[1375.55,216.09],[1376.30,220.02],[1377.03,223.95],[1377.67,227.89],[1378.40,231.82],[1379.08,235.75],[1379.78,239.68],[1380.69,243.55],[1384.08,245.25],[1388.05,245.51],[1392.05,245.51],[1396.04,245.51],[1400.04,245.51],[1404.03,245.51],[1408.03,245.51],[1412.02,245.51],[1416.02,245.51],[1420.01,245.51],[1424.01,245.51],[1428.00,245.51],[1432.00,245.51],[1435.99,245.51],[1439.99,245.51],[1443.98,245.51],[1447.98,245.51],[1451.97,245.51],[1455.97,245.51],[1459.96,245.51],[1463.96,245.51],[1467.95,245.51],[1471.95,245.51],[1475.94,245.51],[1479.94,245.51],[1483.93,245.51],[1487.93,245.51],[1491.92,245.51],[1495.92,245.51],[1499.91,245.51],[1503.91,245.51],[1507.90,245.51],[1511.90,245.51],[1515.89,245.51],[1519.89,245.51],[1523.88,245.51],[1527.88,245.51],[1531.87,245.51],[1535.87,245.51],[1539.86,245.51],[1543.86,245.51],[1547.85,245.51],[1551.85,245.51],[1555.84,245.51],[1559.84,245.47],[1563.25,243.96],[1563.06,240.01],[1562.79,236.04],[1562.09,232.11],[1561.38,228.18],[1560.65,224.25],[1559.92,220.32],[1559.19,216.40],[1558.49,212.46],[1557.78,208.53],[1557.08,204.60],[1556.17,200.71],[1553.07,198.68],[1549.09,198.53],[1545.10,198.53],[1541.10,198.53],[1537.11,198.53],[1533.11,198.53],[1529.12,198.53],[1525.12,198.53],[1521.13,198.53],[1517.13,198.53],[1513.14,198.53],[1509.14,198.53],[1505.15,198.53],[1501.15,198.53],[1497.16,198.53],[1493.16,198.53],[1489.17,198.53],[1485.17,198.53],[1481.18,198.53],[1477.18,198.53],[1473.19,198.53],[1469.19,198.53],[1465.20,198.53],[1461.20,198.53],[1457.21,198.53],[1453.21,198.53],[1449.22,198.53],[1445.22,198.53],[1441.23,198.53],[1437.23,198.53],[1433.24,198.50],[1429.36,197.62],[1427.70,194.15],[1426.96,190.23],[1426.29,186.29],[1425.59,182.36],[1424.31,178.66],[1420.71,177.29],[1416.71,177.29],[1412.72,177.29],[1408.72,177.29],[1404.73,177.29],[1400.73,177.29],[1396.74,177.29],[1392.74,177.29],[1388.75,177.29],[1384.75,177.29],[1380.76,177.29],[1376.76,177.29],[1372.77,177.29],[1368.77,177.29],[1364.78,177.29],[1360.78,177.29],[1356.79,177.29],[1352.79,177.29],[1348.80,177.29],[1344.80,177.29],[1340.83,176.98],[1337.29,175.46],[1336.39,171.58],[1335.66,167.66],[1335.01,163.72],[1334.28,159.79],[1333.60,155.86],[1332.90,151.92],[1332.20,147.99],[1331.51,144.06],[1330.86,140.12],[1330.13,136.19],[1329.46,132.25],[1328.75,128.32],[1328.05,124.39],[1327.37,120.45],[1326.64,116.53],[1325.98,112.59],[1325.25,108.66],[1324.60,104.72],[1323.90,100.79],[1323.22,96.85],[1322.49,92.93],[1321.86,88.98],[1321.14,85.05],[1320.45,81.12],[1319.75,77.19],[1319.10,73.25],[1318.36,69.32],[1317.71,65.38],[1317.01,61.45],[1316.31,57.52],[1315.60,53.59],[1314.90,49.66],[1314.27,45.71],[1313.57,41.78],[1312.86,37.85],[1312.16,33.92],[1311.49,29.98],[1310.76,26.05],[1310.12,22.11],[1309.39,18.18],[1308.89,14.23],[1308.56,10.26],[1309.02,6.46],[1312.79,5.72],[1316.78,5.72],[1320.78,5.72],[1324.77,5.72],[1328.77,5.72],[1332.76,5.72],[1336.76,5.72],[1340.75,5.72],[1344.75,5.72],[1348.74,5.72],[1352.74,5.72],[1356.73,5.72],[1360.73,5.72],[1364.72,5.72],[1368.72,5.72],[1372.71,5.72],[1376.71,5.72],[1380.70,5.72],[1384.70,5.72],[1388.69,5.72],[1392.69,5.72],[1396.68,5.72],[1400.68,5.72],[1404.67,5.72],[1408.67,5.72],[1412.66,5.72],[1416.66,5.72],[1420.65,5.72],[1424.65,5.72],[1428.64,5.72],[1432.64,5.72],[1436.63,5.72],[1440.63,5.72],[1444.62,5.72],[1448.62,5.72],[1452.61,5.72],[1456.61,5.72],[1460.60,5.72],[1464.60,5.72],[1468.59,5.72],[1472.59,5.72],[1476.58,5.72],[1480.58,5.72],[1484.57,5.72],[1488.57,5.72],[1492.50,6.16],[1494.64,9.23],[1495.37,13.16],[1496.10,17.09],[1496.83,21.01],[1497.54,24.94],[1498.24,28.87],[1498.95,32.81],[1499.65,36.74],[1500.35,40.67],[1500.96,44.61],[1501.28,48.59],[1500.50,52.25],[1496.65,53.10],[1492.66,53.10],[1488.66,53.10],[1484.67,53.10],[1480.67,53.10],[1476.68,53.10],[1472.68,53.10],[1468.69,53.10],[1464.69,53.10],[1460.70,53.10],[1456.70,53.10],[1452.71,53.10],[1448.71,53.10],[1444.72,53.10],[1440.72,53.10],[1436.73,53.10],[1432.73,53.10],[1428.74,53.10],[1424.74,53.10],[1420.75,53.10],[1416.75,53.10],[1412.76,53.10],[1408.76,53.10],[1404.77,53.10],[1400.77,53.10],[1396.78,53.10],[1392.78,53.10],[1388.79,53.10],[1384.79,53.10],[1380.80,53.10],[1376.80,53.10],[1373.22,54.20],[1373.10,58.07],[1373.41,62.04],[1373.91,66.00],[1374.58,69.93],[1375.22,73.88],[1375.94,77.80],[1376.61,81.74],[1377.25,85.68],[1377.98,89.61],[1378.65,93.55],[1379.28,97.49],[1380.04,101.41],[1382.64,104.11],[1386.58,104.58],[1390.58,104.58],[1394.57,104.58],[1398.57,104.58],[1402.56,104.58],[1406.56,104.58],[1410.56,104.58],[1414.55,104.58],[1418.55,104.58],[1422.54,104.58],[1426.54,104.58],[1430.53,104.58],[1434.53,104.58],[1438.52,104.58],[1442.52,104.58],[1446.51,104.58],[1450.51,104.58],[1454.50,104.58],[1458.50,104.58],[1462.49,104.58],[1466.49,104.58],[1470.48,104.58],[1474.48,104.58],[1478.47,104.58],[1482.47,104.58],[1486.46,104.58],[1490.46,104.58],[1494.45,104.58],[1498.43,104.74],[1501.46,106.85],[1502.28,110.75],[1503.01,114.68],[1503.74,118.61],[1504.47,122.53],[1505.18,126.46],[1505.88,130.39],[1506.59,134.32],[1507.29,138.26],[1507.91,142.19],[1508.29,146.16],[1506.87,149.46],[1502.94,149.92],[1498.94,149.92],[1494.95,149.92],[1490.95,149.92],[1486.96,149.92],[1482.96,149.92],[1478.97,149.92],[1474.97,149.92],[1470.98,149.92],[1466.98,149.92],[1462.99,149.92],[1458.99,149.92],[1455.00,149.92],[1451.00,149.92],[1447.01,149.92],[1443.01,149.92],[1439.02,149.92],[1435.02,149.92],[1431.03,149.92],[1427.03,149.92],[1423.04,149.92],[1419.04,149.92],[1415.05,149.92],[1411.05,149.92],[1407.06,149.92],[1403.06,149.92],[1399.07,149.92],[1395.07,149.92],[1391.08,149.92]],
  [[1151.70,230.66],[1155.21,232.58],[1158.76,234.43],[1162.25,236.39],[1165.92,238.00],[1169.61,239.55],[1173.32,241.06],[1177.13,242.30],[1180.94,243.52],[1184.78,244.65],[1188.62,245.78],[1192.49,246.82],[1196.39,247.70],[1200.34,248.40],[1204.30,248.96],[1208.25,249.61],[1212.22,250.00],[1216.18,250.52],[1220.17,250.82],[1224.15,251.17],[1228.15,251.23],[1232.15,251.23],[1236.15,251.23],[1240.16,251.23],[1244.13,250.82],[1248.11,250.49],[1252.07,249.95],[1256.04,249.43],[1260.00,248.85],[1263.93,248.13],[1267.82,247.18],[1271.70,246.19],[1275.55,245.07],[1279.35,243.81],[1283.14,242.52],[1286.88,241.08],[1290.49,239.35],[1294.14,237.72],[1297.65,235.79],[1301.04,233.66],[1304.37,231.44],[1307.70,229.21],[1311.02,226.97],[1314.23,224.58],[1317.25,221.95],[1320.16,219.20],[1322.35,215.92],[1322.82,212.06],[1320.89,208.62],[1317.81,206.06],[1314.72,203.51],[1311.64,200.96],[1308.55,198.41],[1305.46,195.87],[1302.38,193.31],[1299.29,190.76],[1296.20,188.21],[1293.11,185.66],[1289.74,183.56],[1285.83,183.15],[1282.24,184.81],[1279.08,187.26],[1275.80,189.56],[1272.47,191.79],[1268.99,193.76],[1265.41,195.55],[1261.68,196.98],[1257.88,198.27],[1254.05,199.43],[1250.17,200.42],[1246.22,201.02],[1242.25,201.58],[1238.28,202.10],[1234.29,202.21],[1230.28,202.21],[1226.28,202.21],[1222.31,201.78],[1218.33,201.39],[1214.38,200.77],[1210.43,200.14],[1206.56,199.13],[1202.70,198.07],[1198.85,196.95],[1195.09,195.59],[1191.40,194.04],[1187.83,192.22],[1184.31,190.32],[1180.89,188.25],[1177.56,186.02],[1174.32,183.66],[1171.15,181.22],[1167.99,178.77],[1164.22,177.51],[1160.23,177.29],[1156.22,177.29],[1152.22,177.29],[1148.21,177.29],[1144.21,177.29],[1140.21,177.29],[1136.20,177.29],[1132.20,177.29],[1128.19,177.29],[1124.19,177.29],[1120.18,177.29],[1116.18,177.29],[1112.17,177.29],[1108.17,177.29],[1104.16,177.29],[1100.16,177.29],[1096.15,177.29],[1092.15,177.29],[1088.14,177.29],[1084.14,177.29],[1080.14,177.29],[1076.13,177.29],[1072.19,176.61],[1069.17,174.22],[1067.57,170.56],[1066.07,166.84],[1064.65,163.10],[1063.32,159.32],[1062.24,155.47],[1061.06,151.64],[1059.94,147.80],[1058.94,143.92],[1058.15,140.00],[1057.58,136.03],[1056.93,132.08],[1056.21,128.14],[1055.70,124.17],[1055.29,120.20],[1054.98,116.22],[1054.88,112.22],[1054.64,108.24],[1054.48,104.24],[1054.76,100.26],[1054.88,96.27],[1054.96,92.27],[1055.44,88.29],[1056.04,84.34],[1056.57,80.37],[1057.25,76.43],[1058.23,72.55],[1059.34,68.70],[1060.48,64.87],[1061.76,61.07],[1063.23,57.35],[1064.88,53.70],[1066.75,50.16],[1068.78,46.71],[1070.82,43.26],[1073.08,39.96],[1075.47,36.75],[1078.00,33.65],[1080.70,30.69],[1083.49,27.82],[1086.51,25.19],[1089.58,22.62],[1092.77,20.21],[1096.15,18.05],[1099.52,15.89],[1102.96,13.85],[1106.54,12.04],[1110.16,10.34],[1113.88,8.87],[1117.63,7.47],[1121.38,6.07],[1125.22,4.95],[1129.14,4.10],[1133.05,3.28],[1136.97,2.45],[1140.91,1.72],[1144.88,1.23],[1148.85,0.83],[1152.84,0.59],[1156.82,0.20],[1160.81,0.00],[1164.81,0.00],[1168.82,0.00],[1172.79,0.41],[1176.77,0.67],[1180.75,1.06],[1184.74,1.28],[1188.70,1.76],[1192.67,2.31],[1196.59,3.10],[1200.51,3.92],[1204.44,4.71],[1208.36,5.52],[1212.24,6.50],[1216.08,7.63],[1219.90,8.82],[1223.67,10.16],[1227.40,11.63],[1231.09,13.18],[1234.79,14.71],[1238.45,16.33],[1241.98,18.22],[1245.54,20.06],[1248.98,22.10],[1252.32,24.30],[1255.65,26.52],[1258.97,28.76],[1262.25,31.07],[1265.38,33.56],[1268.45,36.13],[1270.83,39.28],[1271.92,43.12],[1272.67,47.06],[1273.34,51.00],[1274.04,54.94],[1274.71,58.89],[1275.38,62.84],[1276.08,66.78],[1276.76,70.73],[1277.42,74.68],[1278.12,78.62],[1278.81,82.56],[1279.54,86.50],[1280.16,90.45],[1280.87,94.39],[1281.58,98.33],[1282.21,102.29],[1282.92,106.23],[1283.61,110.17],[1284.25,114.12],[1284.97,118.06],[1285.65,122.01],[1286.36,125.95],[1287.01,129.90],[1287.70,133.84],[1288.40,137.78],[1288.62,141.77],[1288.83,145.73],[1285.50,147.43],[1281.50,147.47],[1277.49,147.47],[1273.49,147.47],[1269.49,147.47],[1265.48,147.47],[1261.48,147.47],[1257.47,147.47],[1253.47,147.47],[1249.46,147.47],[1245.46,147.47],[1241.45,147.47],[1237.45,147.47],[1233.44,147.47],[1229.44,147.47],[1225.43,147.47],[1221.43,147.47],[1217.42,147.47],[1213.42,147.47],[1209.42,147.47],[1205.41,147.47],[1201.41,147.47],[1197.40,147.47],[1193.40,147.47],[1189.39,147.47],[1185.39,147.47],[1181.39,147.36],[1177.72,145.93],[1176.61,142.12],[1175.90,138.18],[1175.19,134.24],[1174.46,130.30],[1173.70,126.37],[1173.00,122.43],[1172.29,118.49],[1171.59,114.55],[1171.12,110.58],[1170.83,106.59],[1171.69,103.04],[1175.58,102.53],[1179.59,102.53],[1183.59,102.53],[1187.60,102.53],[1191.60,102.53],[1195.61,102.53],[1199.61,102.53],[1203.61,102.53],[1207.62,102.53],[1211.62,102.53],[1215.63,102.53],[1219.63,102.53],[1223.64,102.53],[1227.64,102.53],[1231.61,102.18],[1233.36,99.11],[1232.99,95.13],[1232.48,91.17],[1231.74,87.23],[1231.02,83.29],[1230.31,79.35],[1229.66,75.40],[1228.93,71.47],[1227.95,67.59],[1225.29,64.70],[1222.07,62.31],[1218.60,60.31],[1215.05,58.48],[1211.38,56.86],[1207.69,55.31],[1203.94,53.93],[1200.15,52.63],[1196.28,51.58],[1192.36,50.80],[1188.44,49.99],[1184.49,49.33],[1180.51,49.02],[1176.54,48.61],[1172.53,48.61],[1168.53,48.61],[1164.55,48.96],[1160.55,49.09],[1156.60,49.71],[1152.68,50.50],[1148.77,51.36],[1144.98,52.64],[1141.26,54.13],[1137.61,55.76],[1134.15,57.76],[1130.82,59.99],[1127.78,62.59],[1124.87,65.32],[1122.26,68.36],[1120.00,71.67],[1117.94,75.10],[1116.07,78.64],[1114.50,82.32],[1113.32,86.14],[1112.26,90.00],[1111.29,93.88],[1110.81,97.85],[1110.20,101.80],[1110.03,105.80],[1109.92,109.79],[1110.00,113.76],[1110.03,117.76],[1110.28,121.75],[1110.85,125.70],[1111.38,129.67],[1112.00,133.62],[1112.96,137.51],[1114.12,141.34]],
  [[60.87,135.62],[59.74,131.79],[58.83,127.90],[58.21,123.96],[57.68,120.00],[57.19,116.04],[57.18,112.05],[56.87,108.08],[57.19,104.12],[57.50,100.15],[58.04,96.20],[58.82,92.29],[59.93,88.46],[61.18,84.67],[62.75,81.00],[64.69,77.51],[66.90,74.18],[69.24,70.94],[71.81,67.90],[74.65,65.08],[77.76,62.60],[81.05,60.32],[84.43,58.20],[88.01,56.43],[91.70,54.90],[95.43,53.48],[99.31,52.52],[103.21,51.66],[107.13,50.93],[111.11,50.65],[115.07,50.25],[119.07,50.25],[123.05,50.35],[127.03,50.66],[130.99,51.10],[134.89,51.93],[138.81,52.68],[142.69,53.62],[146.53,54.72],[150.25,56.18],[153.96,57.66],[157.63,59.23],[161.25,60.92],[164.80,62.75],[168.20,64.84],[171.55,67.02],[174.89,69.21],[178.39,71.09],[182.28,71.87],[185.78,70.07],[188.32,67.00],[190.67,63.77],[193.06,60.57],[195.45,57.36],[197.82,54.15],[200.20,50.94],[202.57,47.73],[204.91,44.49],[207.13,41.17],[208.62,37.51],[207.99,33.73],[205.37,30.74],[202.18,28.34],[198.92,26.03],[195.57,23.86],[192.17,21.75],[188.78,19.64],[185.25,17.77],[181.68,15.99],[178.10,14.21],[174.46,12.58],[170.75,11.10],[167.04,9.62],[163.32,8.14],[159.50,7.00],[155.67,5.88],[151.78,4.95],[147.87,4.13],[143.96,3.30],[140.05,2.52],[136.11,1.89],[132.14,1.43],[128.18,1.03],[124.21,0.75],[120.24,0.41],[116.27,0.03],[112.28,0.00],[108.28,0.00],[104.30,0.16],[100.33,0.49],[96.36,0.82],[92.39,1.21],[88.43,1.71],[84.50,2.38],[80.59,3.20],[76.69,4.06],[72.79,4.94],[68.95,6.03],[65.15,7.28],[61.44,8.76],[57.74,10.26],[54.15,12.02],[50.58,13.80],[47.05,15.67],[43.63,17.73],[40.30,19.94],[37.07,22.29],[34.01,24.86],[31.00,27.48],[28.14,30.27],[25.40,33.18],[22.77,36.18],[20.34,39.35],[17.94,42.54],[15.74,45.87],[13.71,49.31],[11.85,52.85],[10.09,56.43],[8.48,60.08],[7.15,63.85],[5.88,67.64],[4.65,71.44],[3.48,75.25],[2.60,79.15],[2.03,83.10],[1.34,87.03],[0.81,90.98],[0.42,94.94],[0.07,98.91],[0.00,102.90],[0.00,106.90],[0.00,110.89],[0.03,114.88],[0.41,118.85],[0.91,122.81],[1.55,126.75],[2.12,130.70],[2.82,134.63],[3.53,138.56],[4.48,142.44],[5.58,146.28],[6.75,150.09],[8.02,153.88],[9.27,157.68],[10.60,161.44],[12.20,165.10],[13.83,168.75],[15.60,172.33],[17.76,175.64],[21.46,177.01],[25.44,177.29],[29.43,177.29],[33.43,177.29],[37.42,177.29],[41.42,177.29],[45.41,177.29],[49.41,177.29],[53.40,177.29],[57.40,177.29],[61.39,177.29],[65.39,177.29],[69.38,177.29],[73.38,177.29],[77.37,177.29],[81.36,177.29],[85.36,177.29],[89.35,177.29],[93.35,177.29],[97.34,177.29],[101.34,177.29],[105.33,177.29],[109.33,177.29],[113.32,177.29],[117.23,178.01],[120.72,179.86],[123.79,182.41],[127.06,184.71],[130.35,186.97],[133.70,189.16],[137.15,191.16],[140.70,192.99],[144.33,194.66],[148.05,196.11],[151.85,197.32],[155.65,198.55],[159.55,199.41],[163.49,200.08],[167.44,200.59],[171.40,200.98],[175.39,201.02],[179.35,201.01],[183.35,200.98],[187.31,200.62],[191.26,200.04],[195.21,199.49],[199.06,198.43],[202.90,197.34],[206.67,196.02],[210.31,194.39],[213.84,192.51],[217.19,190.34],[220.50,188.10],[223.74,185.77],[226.96,183.44],[230.81,182.56],[234.60,183.75],[237.63,186.35],[240.55,189.07],[243.54,191.71],[246.43,194.47],[249.41,197.13],[252.34,199.84],[255.26,202.56],[258.25,205.21],[261.15,207.96],[263.66,210.98],[264.33,214.83],[262.72,218.45],[259.92,221.29],[256.90,223.91],[253.82,226.45],[250.69,228.93],[247.46,231.28],[244.09,233.42],[240.68,235.50],[237.22,237.50],[233.65,239.29],[230.00,240.91],[226.36,242.54],[222.60,243.89],[218.82,245.20],[214.97,246.24],[211.10,247.23],[207.22,248.18],[203.29,248.88],[199.34,249.43],[195.39,249.96],[191.43,250.45],[187.46,250.82],[183.47,250.82],[179.47,250.82],[175.48,250.82],[171.48,250.82],[167.52,250.41],[163.55,250.01],[159.60,249.46],[155.64,248.92],[151.68,248.37],[147.76,247.66],[143.86,246.80],[139.99,245.81],[136.16,244.66],[132.35,243.48],[128.52,242.34],[124.74,241.04],[121.02,239.59],[117.35,238.01],[113.69,236.40],[110.12,234.62],[106.62,232.71]],
  [[322.30,152.64],[326.30,152.78],[330.30,152.78],[334.31,152.78],[338.31,152.78],[342.31,152.78],[346.32,152.78],[350.32,152.78],[354.33,152.78],[358.33,152.78],[362.33,152.78],[366.34,152.78],[370.34,152.78],[374.35,152.78],[378.35,152.78],[382.35,152.78],[386.36,152.78],[390.36,152.78],[394.36,152.78],[398.37,152.78],[402.37,152.78],[406.38,152.78],[410.38,152.78],[414.38,152.78],[418.36,153.07],[421.00,155.76],[421.80,159.68],[422.45,163.63],[423.19,167.56],[423.85,171.51],[424.85,175.34],[428.33,177.01],[432.31,177.29],[436.32,177.29],[440.32,177.29],[444.32,177.29],[448.33,177.29],[452.33,177.29],[456.34,177.29],[460.34,177.29],[464.34,177.29],[468.35,177.29],[472.35,177.29],[476.35,177.29],[480.36,177.29],[484.36,177.29],[488.37,177.29],[492.37,177.29],[496.37,177.29],[500.38,177.29],[504.38,177.29],[508.39,177.29],[512.34,177.68],[514.63,180.64],[515.35,184.58],[515.99,188.53],[516.72,192.47],[517.45,196.41],[518.09,200.36],[518.81,204.29],[519.51,208.24],[520.21,212.18],[520.92,216.12],[521.58,220.06],[522.31,224.00],[522.96,227.95],[523.69,231.88],[524.41,235.82],[524.60,239.82],[524.76,243.78],[521.46,245.46],[517.46,245.51],[513.45,245.51],[509.45,245.51],[505.45,245.51],[501.44,245.51],[497.44,245.51],[493.44,245.51],[489.43,245.51],[485.43,245.51],[481.42,245.51],[477.42,245.51],[473.42,245.43],[469.58,244.49],[468.11,240.90],[467.37,236.96],[466.70,233.02],[465.99,229.08],[465.29,225.14],[464.60,221.19],[463.95,217.24],[463.22,213.31],[462.54,209.36],[461.60,205.47]],
  [[646.65,171.57],[649.43,168.74],[651.08,165.18],[652.26,161.38],[653.49,157.61],[654.64,153.81],[655.85,150.03],[657.05,146.25],[658.28,142.47],[659.43,138.67],[660.64,134.89],[661.87,131.12],[663.04,127.33],[664.26,123.55],[665.42,119.75],[666.67,115.98],[667.80,112.18],[668.99,108.39],[669.50,104.46],[669.88,100.53],[667.14,98.45],[663.17,98.45],[659.20,98.45],[655.23,98.45],[651.26,98.45],[647.29,98.45],[643.32,98.45],[639.35,98.45],[635.38,98.45],[631.41,98.45],[627.44,98.45],[623.47,98.45],[619.50,98.45],[615.53,98.45],[611.56,98.45],[607.59,98.45],[603.62,98.45],[600.66,100.13],[601.40,104.00],[602.40,107.84]],
  [[658.09,244.42],[661.96,245.38],[665.95,245.51],[669.94,245.51],[673.94,245.51],[677.94,245.51],[681.93,245.51],[685.93,245.51],[689.93,245.51],[693.92,245.51],[697.92,245.51],[701.92,245.51],[705.91,245.51],[709.91,245.51],[713.90,245.43],[717.72,244.35],[719.34,240.79],[720.37,236.93],[721.40,233.07],[722.42,229.20],[723.46,225.34],[724.50,221.48],[725.57,217.64],[726.64,213.79],[727.71,209.94],[728.77,206.09],[729.76,202.21],[730.78,198.35],[731.84,194.50],[732.90,190.65],[733.95,186.79],[734.45,182.83],[734.76,178.88],[731.65,177.29],[727.66,177.29],[723.66,177.29],[719.66,177.29],[715.67,177.29],[711.67,177.29],[707.67,177.29],[703.68,177.29],[699.68,177.29],[695.68,177.29],[691.69,177.29],[687.69,177.29],[683.69,177.29],[679.70,177.29],[675.70,177.29],[671.70,177.29],[667.70,177.29],[663.71,177.29],[659.71,177.29],[655.71,177.29],[651.72,177.29],[647.96,176.15],[644.34,175.98],[640.73,177.29],[636.73,177.29],[632.74,177.29],[628.74,177.29],[624.74,177.29],[620.74,177.29],[616.75,177.29],[612.75,177.29],[608.75,177.29],[604.76,177.29],[600.76,177.29],[596.76,177.29],[592.77,177.29],[588.77,177.26],[584.88,176.41],[582.59,173.21],[580.45,169.84],[578.30,166.46],[576.16,163.09],[574.02,159.72],[571.87,156.35],[569.73,152.97],[567.59,149.60],[565.44,146.23],[563.30,142.85],[561.17,139.47],[559.04,136.09],[556.90,132.71],[554.77,129.33],[552.64,125.95],[550.50,122.57],[548.37,119.19],[546.23,115.81],[544.10,112.43],[541.97,109.05],[539.84,105.67],[537.71,102.29],[535.58,98.91],[533.45,95.52],[531.32,92.14],[529.19,88.76],[527.06,85.38],[524.93,82.00],[522.80,78.61],[520.68,75.23],[518.56,71.84],[516.43,68.46],[514.31,65.07],[512.19,61.68],[510.06,58.30],[507.94,54.91],[505.82,51.53],[503.69,48.14],[501.57,44.75],[499.46,41.36],[497.35,37.97],[495.23,34.58],[493.12,31.18],[491.01,27.79],[488.89,24.40],[486.78,21.01],[484.67,17.61],[482.66,14.17],[481.61,10.32],[481.05,6.41],[484.86,5.72],[488.85,5.72],[492.85,5.72],[496.85,5.72],[500.84,5.72],[504.84,5.72],[508.84,5.72],[512.83,5.72],[516.83,5.72],[520.83,5.72],[524.82,5.72],[528.82,5.72],[532.82,5.72],[536.81,5.72],[540.72,6.37],[543.58,9.11],[545.75,12.47],[547.78,15.91],[549.81,19.35],[551.85,22.79],[553.88,26.23],[555.92,29.67],[557.96,33.10],[559.98,36.55],[562.03,39.98],[564.09,43.41],[566.43,46.65],[570.00,48.17],[573.96,48.61],[577.95,48.61],[581.95,48.61],[585.95,48.61],[589.94,48.61],[593.94,48.61],[597.94,48.61],[601.93,48.61],[605.93,48.61],[609.93,48.61],[613.92,48.61],[617.92,48.61],[621.92,48.61],[625.91,48.61],[629.91,48.61],[633.91,48.61],[637.90,48.61],[641.90,48.61],[645.90,48.61],[649.89,48.61],[653.89,48.61],[657.89,48.61],[661.89,48.61],[665.88,48.61],[669.88,48.61],[673.88,48.61],[677.87,48.61],[681.81,47.98],[684.49,45.31],[685.48,41.44],[686.44,37.56],[687.39,33.68],[688.38,29.80],[689.36,25.93],[690.29,22.04],[691.28,18.17],[692.27,14.30],[693.18,10.41],[694.82,6.88],[698.55,5.72],[702.54,5.72],[706.54,5.72],[710.54,5.72],[714.53,5.72],[718.53,5.72],[722.53,5.72],[726.52,5.72],[730.52,5.72],[734.52,5.72],[738.51,5.72],[742.51,5.72],[746.51,5.72],[749.91,7.04],[749.61,11.01],[749.09,14.97],[748.10,18.84],[747.03,22.69],[745.96,26.54],[744.90,30.39],[743.93,34.26],[742.88,38.12],[741.82,41.97],[740.78,45.83],[739.74,49.69],[738.69,53.55],[737.63,57.40],[736.56,61.25],[735.51,65.10],[734.48,68.96],[733.46,72.83],[732.43,76.69],[731.37,80.54],[730.30,84.39],[729.23,88.24],[728.24,92.11],[727.17,95.96],[726.10,99.81],[725.03,103.66],[724.00,107.52],[722.97,111.38],[721.95,115.25],[720.90,119.10],[719.83,122.95],[718.76,126.80],[717.72,130.66],[716.68,134.52],[715.64,138.38],[714.59,142.23],[713.54,146.09],[712.42,149.92]],
  [[476.58,146.24],[475.75,142.34],[475.07,138.40],[474.36,134.47],[473.66,130.54],[472.98,126.60],[472.25,122.67],[471.62,118.73],[470.92,114.79],[470.21,110.86],[469.51,106.93],[468.86,102.99],[468.13,99.06],[467.47,95.12],[466.77,91.19],[466.08,87.25],[465.36,83.32],[464.73,79.37],[464.03,75.44],[463.32,71.51],[462.62,67.58],[461.91,63.64],[461.25,59.70],[460.58,55.77],[459.88,51.83],[459.17,47.90],[458.48,43.97],[457.76,40.04],[457.12,36.09],[456.39,32.17],[455.73,28.22],[455.02,24.29],[454.35,20.35],[453.62,16.43],[452.97,12.48],[452.17,8.57],[449.55,5.93],[445.57,5.72],[441.58,5.72],[437.58,5.72],[433.58,5.72],[429.59,5.72],[425.59,5.72],[421.60,5.72],[417.60,5.72],[413.60,5.72],[409.61,5.72],[405.61,5.72],[401.61,5.72],[397.63,5.90],[396.14,9.08],[396.32,13.07],[396.81,17.03],[397.53,20.95],[398.19,24.90],[398.90,28.83],[399.57,32.77],[400.30,36.69],[400.94,40.64],[401.64,44.57],[402.33,48.50],[402.98,52.45],[403.71,56.38],[404.37,60.32],[405.09,64.25],[405.75,68.19],[406.48,72.11],[407.12,76.06],[407.83,79.99],[408.52,83.92],[409.16,87.87],[409.87,91.80],[410.15,95.78],[410.50,99.74],[407.65,101.89],[403.67,102.12],[399.67,102.12],[395.68,102.12],[391.68,102.12],[387.68,102.12],[383.69,102.12],[379.69,102.12],[375.70,102.12],[371.70,102.12],[367.70,102.12],[363.71,102.12],[359.71,102.12],[355.71,102.12],[351.72,102.12],[347.72,102.12],[343.73,102.12],[339.73,102.12],[335.73,102.12],[331.74,102.12],[327.74,102.12],[323.75,102.12],[319.75,102.12],[315.76,102.02],[311.89,101.13],[310.10,97.78],[309.45,93.83],[308.72,89.91],[308.06,85.96],[307.34,82.04],[306.68,78.10],[306.01,74.16],[305.30,70.22],[304.65,66.28],[303.92,62.36],[303.27,58.41],[302.54,54.48],[301.88,50.54],[301.15,46.62],[300.51,42.67],[299.82,38.74],[299.12,34.80],[298.47,30.86],[297.73,26.94],[297.08,22.99],[296.38,19.06],[295.70,15.12],[294.97,11.20],[293.98,7.35],[290.53,5.75],[286.54,5.72],[282.54,5.72],[278.54,5.72],[274.55,5.72],[270.55,5.72],[266.56,5.72],[262.56,5.72],[258.56,5.72],[254.57,5.72],[250.57,5.72],[246.57,5.72],[242.58,5.72],[238.69,6.27],[238.15,10.08],[238.46,14.05],[238.98,18.00],[239.68,21.94],[240.31,25.88],[241.04,29.81],[241.72,33.75],[242.42,37.68],[243.13,41.61],[243.81,45.55],[244.53,49.48],[245.16,53.42],[245.87,57.36],[246.57,61.29],[247.28,65.22],[247.92,69.16],[248.65,73.09],[249.31,77.03],[250.03,80.96],[250.69,84.90],[251.42,88.83],[252.07,92.77],[252.80,96.70],[253.46,100.64],[254.18,104.57],[254.87,108.51],[255.56,112.44],[256.22,116.38],[256.95,120.31],[257.61,124.25],[258.33,128.18],[259.02,132.11],[259.71,136.05],[260.43,139.98],[261.10,143.92],[261.76,147.86],[262.47,151.79],[263.17,155.72],[263.86,159.66],[264.58,163.59],[265.23,167.53],[265.97,171.46],[266.83,175.35],[270.29,176.97],[274.26,177.29],[278.26,177.29],[282.25,177.29],[286.25,177.29],[290.25,177.29],[294.24,177.29],[298.24,177.29],[302.24,177.29],[306.23,177.29],[310.23,177.29],[314.22,177.29],[318.22,177.29],[322.22,177.29],[326.21,177.29],[330.21,177.29],[334.21,177.29],[338.20,177.29],[342.20,177.29],[346.19,177.29],[350.19,177.29],[354.11,177.81],[356.20,180.94],[356.91,184.87],[357.61,188.81],[358.32,192.74],[359.02,196.67],[359.73,200.60],[360.36,204.55],[361.08,208.48],[361.76,212.41],[362.47,216.35],[363.17,220.28],[363.88,224.21],[364.58,228.14],[365.29,232.08],[365.93,236.02],[366.21,240.00],[366.27,243.97],[362.78,245.46],[358.78,245.51],[354.79,245.51],[350.79,245.51],[346.80,245.51],[342.80,245.51],[338.80,245.51],[334.81,245.51],[330.81,245.51],[326.81,245.51],[322.82,245.51],[318.82,245.51],[314.83,245.42],[311.03,244.41],[309.60,240.82],[308.90,236.89],[308.20,232.95],[307.49,229.02],[306.83,225.08],[306.10,221.15],[305.45,217.21],[304.75,213.28],[304.07,209.34],[303.10,205.47]],
  [[990.99,5.72],[986.98,5.72],[982.98,5.72],[978.97,5.72],[974.97,5.72],[970.96,5.72],[966.96,5.72],[962.95,5.72],[958.95,5.72],[954.94,5.72],[950.94,5.72],[946.93,5.72],[942.92,5.72],[938.92,5.72],[934.92,5.80],[931.23,7.19],[928.93,10.45],[926.85,13.88],[924.78,17.30],[922.70,20.73],[920.62,24.15],[918.55,27.58],[916.48,31.01],[914.41,34.44],[912.34,37.87],[910.26,41.29],[908.18,44.71],[906.10,48.13],[904.02,51.56],[901.93,54.97],[899.83,58.39],[897.74,61.80],[895.65,65.22],[893.55,68.63],[891.45,72.04],[889.34,75.45],[887.24,78.86],[885.00,82.17],[881.18,83.22],[877.19,83.33],[873.18,83.33],[869.18,83.33],[865.17,83.33],[861.17,83.33],[857.16,83.33],[853.16,83.33],[849.19,82.83],[846.61,80.17],[845.86,76.24],[845.16,72.29],[844.45,68.35],[843.82,64.40],[843.11,60.46],[842.41,56.52],[841.70,52.58],[840.99,48.64],[840.32,44.69],[839.59,40.75],[838.95,36.80],[838.22,32.86],[837.54,28.91],[836.83,24.97],[836.13,21.03],[835.45,17.08],[834.72,13.15],[834.07,9.20],[831.75,6.18],[827.80,5.72],[823.80,5.72],[819.79,5.72],[815.79,5.72],[811.78,5.72],[807.78,5.72],[803.77,5.72],[799.77,5.72],[795.76,5.72],[791.76,5.72],[787.75,5.72],[783.75,5.72],[779.75,5.79],[777.75,8.61],[777.98,12.60],[778.43,16.57],[779.16,20.51],[779.81,24.46],[780.55,28.39],[781.20,32.34],[781.93,36.28],[782.58,40.23],[783.32,44.17],[783.97,48.12],[784.70,52.06],[785.36,56.01],[786.08,59.94],[786.77,63.89],[787.47,67.83],[788.13,71.78],[788.86,75.72],[789.52,79.67],[790.23,83.61],[790.93,87.55],[791.63,91.49],[792.34,95.43],[792.99,99.38],[793.68,103.33],[794.39,107.27],[795.09,111.21],[795.77,115.16],[796.50,119.09],[797.13,123.05],[797.84,126.99],[798.55,130.93],[799.25,134.87],[799.88,138.83],[800.61,142.76],[801.29,146.71],[802.00,150.65],[802.71,154.59],[803.39,158.54],[804.04,162.49],[804.75,166.43],[805.45,170.37],[806.24,174.29],[809.10,176.78],[813.06,177.29],[817.07,177.29],[821.07,177.29],[825.08,177.29],[829.08,177.29],[833.09,177.29],[837.09,177.29],[841.10,177.29],[845.10,177.29],[849.11,177.29],[853.11,177.29],[857.12,177.29],[861.12,177.29],[865.13,177.29],[869.13,177.29],[873.14,177.29],[877.15,177.29],[881.15,177.29],[885.16,177.29],[889.16,177.29],[893.09,177.86],[895.22,180.98],[895.90,184.92],[896.64,188.86],[897.28,192.81],[898.83,196.38],[902.59,197.51],[906.58,197.71],[910.58,197.71],[914.59,197.71],[918.59,197.71],[922.60,197.71],[926.60,197.71],[930.61,197.71],[934.61,197.71],[938.62,197.71],[942.62,197.71],[946.63,197.71],[950.64,197.71],[954.63,197.58]],
  [[992.08,6.94],[991.08,10.80],[990.10,14.64],[987.99,18.02],[985.86,21.39],[983.73,24.77],[981.61,28.14],[979.47,31.50],[977.33,34.86],[975.19,38.23],[973.05,41.59],[970.92,44.96],[968.80,48.34],[966.67,51.71],[964.55,55.08],[962.42,58.45],[960.30,61.83],[958.17,65.20],[956.04,68.57],[953.92,71.94],[951.79,75.31],[949.67,78.69],[947.70,82.12],[946.75,85.99],[947.88,89.56],[951.49,91.15],[955.19,92.65],[958.88,94.14],[962.46,95.90],[966.08,97.56],[969.50,99.61],[972.91,101.66],[976.30,103.77],[979.52,106.11],[982.60,108.65],[985.55,111.31],[988.47,114.02],[991.12,117.00],[993.68,120.06],[995.99,123.30],[998.17,126.64],[1000.29,130.01],[1002.23,133.49],[1003.89,137.12],[1005.44,140.79],[1006.85,144.51],[1008.14,148.28]],
  [[859.04,154.41],[858.34,150.47],[857.63,146.52],[856.92,142.58],[856.49,138.60],[856.16,134.62],[856.39,130.76],[860.14,129.90],[864.15,129.90],[868.16,129.90],[872.17,129.90],[876.17,129.90],[880.18,129.90],[884.19,129.90],[888.20,129.90],[892.21,129.90],[896.22,129.90],[900.23,129.90],[904.24,129.90],[908.25,129.90],[912.25,129.90],[916.26,129.90],[920.24,130.30],[924.19,130.96],[928.11,131.74],[931.85,133.17],[935.53,134.75],[938.98,136.79],[942.23,139.14],[945.06,141.95],[947.77,144.90],[949.97,148.25],[951.94,151.74],[953.44,155.45],[954.67,159.27],[955.49,163.19],[955.90,167.16],[956.27,171.14],[956.13,175.13],[959.24,177.07],[963.24,177.29],[967.25,177.29],[971.25,177.29],[975.26,177.29],[979.27,177.29],[983.28,177.29],[987.29,177.29],[991.30,177.29],[995.31,177.29],[999.32,177.29],[1003.32,177.29],[1007.33,177.29],[1011.34,177.29],[1015.35,177.29],[1019.36,177.29],[1023.37,177.29],[1027.38,177.29],[1031.39,177.29],[1035.40,177.29],[1039.40,177.30],[1042.59,179.32],[1042.51,183.25],[1042.20,187.24],[1041.39,191.16],[1040.58,195.08],[1039.44,198.92],[1037.95,202.65],[1036.40,206.34],[1034.62,209.92],[1032.60,213.39],[1030.35,216.70],[1027.88,219.86],[1025.15,222.79],[1022.31,225.62],[1019.35,228.32],[1016.15,230.73],[1012.80,232.93],[1009.32,234.91],[1005.78,236.80],[1002.20,238.60],[998.45,240.02],[994.63,241.23],[990.78,242.33],[986.91,243.36],[982.95,243.93],[979.00,244.56],[975.03,245.07],[971.02,245.11],[967.04,245.50],[963.04,245.51],[959.03,245.51],[955.02,245.51],[951.01,245.51],[947.00,245.51],[942.99,245.51],[938.98,245.51],[934.97,245.51],[930.97,245.51],[926.96,245.51],[922.95,245.51],[918.94,245.51],[914.93,245.51],[910.92,245.51],[906.91,245.51],[902.90,245.51],[898.90,245.51],[894.89,245.51],[890.88,245.51],[886.87,245.51],[882.86,245.51],[878.85,245.51],[874.84,245.51],[870.83,245.51],[866.82,245.51],[862.82,245.51],[858.81,245.51],[854.80,245.51],[850.79,245.51],[846.78,245.51],[842.77,245.51],[838.76,245.51],[834.75,245.51],[830.75,245.51],[826.75,245.34],[824.55,242.67],[824.95,238.69],[825.34,234.71],[826.18,230.79],[827.01,226.87],[827.91,222.97],[828.76,219.05],[829.63,215.14],[830.51,211.22],[831.35,207.31],[832.35,203.43]]
];
wl_piece_segs = [[2], [3, 6], [4, 5], [7, 8, 9], [1], [0]];
wl_piece_px = [
  [[60.87,135.62],[57.56,119.04],[57.34,102.16],[60.86,85.64],[69.20,70.99],[81.82,59.84],[97.25,53.03],[113.94,50.36],[130.84,51.08],[147.30,55.02],[162.84,61.74],[177.31,70.51],[190.57,63.91],[200.67,50.31],[208.33,35.74],[196.46,24.43],[181.77,16.03],[166.23,9.30],[149.99,4.58],[133.33,1.57],[116.47,0.05],[99.55,0.56],[82.77,2.74],[66.35,6.88],[50.85,13.66],[36.57,22.71],[24.34,34.39],[14.43,48.10],[7.30,63.43],[2.53,79.66],[0.29,96.45],[0.02,113.37],[2.04,130.18],[5.71,146.70],[11.16,162.72],[20.01,176.47],[36.85,177.29],[53.78,177.29],[70.72,177.29],[87.66,177.29],[104.60,177.29],[120.94,180.05],[134.78,189.79],[150.16,196.78],[166.65,200.49],[183.56,200.96],[200.21,198.10],[215.65,191.34],[230.03,182.74],[243.68,191.84],[256.13,203.33],[263.41,216.90],[251.26,228.48],[237.01,237.60],[221.46,244.28],[205.09,248.56],[188.30,250.74],[171.36,250.81],[154.55,248.77],[138.01,245.22],[121.92,239.94],[106.62,232.71]],
  [[322.30,152.64],[339.16,152.78],[356.03,152.78],[372.90,152.78],[389.76,152.78],[406.63,152.78],[421.27,157.09],[424.41,173.66],[439.59,177.29],[456.45,177.29],[473.32,177.29],[490.19,177.29],[506.25,177.29],[516.10,189.13],[518.93,204.95],[521.86,221.56],[524.45,236.59],[512.29,245.51],[497.02,245.51],[480.96,245.51],[467.54,237.86],[464.75,222.03],[461.60,205.47],[476.58,146.24],[473.50,129.61],[470.59,112.95],[467.67,96.29],[464.77,79.63],[461.80,62.98],[458.89,46.32],[455.97,29.66],[453.18,13.79],[440.08,5.72],[423.96,5.72],[408.65,5.72],[396.51,14.64],[399.06,29.74],[401.96,46.40],[404.87,63.07],[407.78,79.73],[410.14,95.65],[396.82,102.12],[380.70,102.12],[363.79,102.12],[346.88,102.12],[329.96,102.12],[313.12,101.41],[308.08,86.10],[305.17,69.44],[302.25,52.78],[299.35,36.12],[296.45,19.45],[289.78,5.74],[272.87,5.72],[255.95,5.72],[239.07,6.22],[239.79,22.64],[242.71,39.30],[245.62,55.96],[248.56,72.62],[251.49,89.28],[254.42,105.93],[257.33,122.59],[260.30,139.25],[263.20,155.91],[266.21,172.55],[280.50,177.29],[297.42,177.29],[314.33,177.29],[331.24,177.29],[347.36,177.29],[357.60,188.78],[360.38,204.65],[363.35,221.30],[365.96,236.39],[354.05,245.51],[338.74,245.51],[322.62,245.51],[309.09,237.94],[306.27,222.07],[303.10,205.47]],
  [[649.78,167.98],[654.54,154.13],[658.98,140.15],[664.15,123.88],[668.52,109.88],[658.19,98.45],[643.52,98.45],[628.85,98.45],[614.18,98.45],[602.40,107.84],[658.09,244.42],[674.91,245.51],[691.85,245.51],[707.99,245.51],[720.56,236.20],[724.74,220.61],[729.23,204.28],[733.01,190.24],[724.93,177.29],[710.39,177.29],[693.45,177.29],[676.51,177.29],[661.17,177.29],[638.24,177.29],[623.70,177.29],[608.36,177.29],[592.22,177.29],[579.60,168.50],[570.51,154.21],[561.44,139.90],[552.40,125.58],[543.36,111.25],[534.33,96.92],[525.30,82.59],[516.29,68.24],[507.30,53.89],[498.32,39.52],[489.36,25.15],[482.01,11.78],[495.67,5.72],[511.01,5.72],[527.95,5.72],[543.66,9.24],[552.41,23.74],[561.04,38.32],[573.11,48.52],[590.04,48.61],[606.98,48.61],[623.92,48.61],[640.86,48.61],[657.80,48.61],[673.94,48.61],[686.16,38.68],[690.06,23.02],[694.88,6.86],[711.64,5.72],[728.58,5.72],[744.72,5.72],[747.80,19.93],[743.59,35.51],[739.15,51.86],[734.68,68.20],[730.25,84.55],[725.80,100.89],[721.40,117.25],[716.93,133.59],[712.42,149.92]],
  [[966.66,5.72],[951.94,5.72],[937.21,5.75],[925.77,15.67],[917.72,28.95],[908.85,43.60],[899.93,58.22],[890.97,72.82],[879.11,83.28],[861.99,83.33],[846.50,79.59],[843.52,62.72],[840.52,45.86],[837.55,28.99],[834.55,12.13],[821.43,5.72],[804.30,5.72],[788.77,5.72],[778.41,16.42],[781.10,31.72],[784.06,48.59],[787.05,65.45],[790.00,82.32],[792.96,99.19],[795.94,116.05],[798.90,132.92],[801.85,149.79],[804.65,165.88],[815.44,177.29],[831.77,177.29],[848.89,177.29],[866.02,177.29],[882.35,177.29],[895.79,184.30],[904.05,197.58],[920.38,197.71],[937.51,197.71],[954.63,197.58],[989.23,16.04],[981.64,28.09],[973.14,41.45],[965.55,53.49],[957.10,66.89],[949.53,78.94],[955.66,92.84],[969.16,99.41],[981.59,107.82],[992.78,118.98],[1001.89,132.88],[1008.14,148.28],[859.04,154.41],[856.53,138.95],[868.55,129.90],[884.22,129.90],[901.49,129.90],[918.75,130.15],[935.31,134.66],[948.33,145.75],[955.13,161.48],[959.14,177.01],[976.39,177.29],[993.66,177.29],[1010.93,177.29],[1028.20,177.29],[1042.54,181.61],[1039.55,198.56],[1032.12,214.10],[1020.76,227.04],[1006.36,236.49],[990.22,242.48],[973.19,245.09],[955.94,245.51],[938.67,245.51],[921.39,245.51],[904.12,245.51],[886.85,245.51],[869.58,245.51],[852.31,245.51],[836.64,245.51],[825.25,235.59],[828.50,220.26],[832.35,203.43]],
  [[1151.70,230.66],[1166.80,238.37],[1182.78,244.06],[1199.22,248.20],[1216.03,250.50],[1232.98,251.23],[1249.90,250.25],[1266.63,247.47],[1282.88,242.61],[1298.23,235.42],[1312.33,225.99],[1322.67,213.28],[1311.80,201.10],[1298.71,190.29],[1284.19,183.91],[1270.03,193.17],[1254.27,199.36],[1237.55,202.12],[1220.61,201.61],[1203.97,198.42],[1188.16,192.39],[1173.85,183.30],[1158.63,177.29],[1141.66,177.29],[1124.69,177.29],[1107.72,177.29],[1090.74,177.29],[1073.81,176.89],[1064.83,163.59],[1059.83,147.38],[1056.68,130.72],[1054.92,113.85],[1054.86,96.90],[1056.62,80.05],[1060.89,63.64],[1067.89,48.22],[1077.50,34.26],[1089.71,22.52],[1103.96,13.34],[1119.58,6.74],[1136.03,2.65],[1152.86,0.59],[1169.80,0.10],[1186.71,1.52],[1203.41,4.50],[1219.82,8.79],[1235.58,15.06],[1250.51,23.11],[1264.43,32.80],[1272.63,46.87],[1275.51,63.59],[1278.41,80.31],[1281.34,97.03],[1284.19,113.76],[1287.11,130.48],[1287.40,146.46],[1270.66,147.47],[1253.69,147.47],[1236.72,147.47],[1219.75,147.47],[1202.77,147.47],[1186.60,147.47],[1175.64,136.76],[1172.71,120.85],[1171.43,104.09],[1187.55,102.53],[1204.52,102.53],[1219.89,102.53],[1232.87,94.23],[1230.26,79.08],[1224.23,63.92],[1209.29,55.98],[1193.11,50.95],[1176.33,48.61],[1159.39,49.27],[1142.98,53.44],[1128.45,62.01],[1117.90,75.17],[1112.00,91.01],[1109.97,107.82],[1110.71,124.75],[1114.12,141.34]],
  [[1375.55,216.09],[1378.59,232.91],[1386.53,245.41],[1403.62,245.51],[1420.71,245.51],[1437.80,245.51],[1454.90,245.51],[1471.99,245.51],[1489.08,245.51],[1506.18,245.51],[1523.27,245.51],[1540.37,245.51],[1555.86,245.51],[1561.97,231.46],[1559.16,216.22],[1555.09,200.00],[1538.39,198.53],[1521.30,198.53],[1504.20,198.53],[1487.11,198.53],[1470.02,198.53],[1452.92,198.53],[1436.63,198.53],[1426.51,187.58],[1415.88,177.29],[1399.59,177.29],[1382.49,177.29],[1365.40,177.29],[1349.11,177.29],[1335.92,169.06],[1333.09,153.01],[1330.13,136.17],[1327.16,119.34],[1324.20,102.50],[1321.25,85.67],[1318.28,68.84],[1315.32,52.00],[1312.38,35.16],[1309.71,19.90],[1315.70,5.72],[1331.19,5.72],[1348.28,5.72],[1365.38,5.72],[1382.47,5.72],[1399.57,5.72],[1416.66,5.72],[1433.75,5.72],[1450.85,5.72],[1467.94,5.72],[1484.23,5.72],[1495.85,15.78],[1498.77,31.81],[1501.25,48.70],[1487.12,53.10],[1470.03,53.10],[1452.93,53.10],[1435.84,53.10],[1418.75,53.10],[1401.65,53.10],[1386.16,53.10],[1373.36,61.38],[1375.73,76.68],[1378.51,92.74],[1388.75,104.58],[1405.04,104.58],[1422.13,104.58],[1439.23,104.58],[1456.32,104.58],[1473.42,104.58],[1489.71,104.58],[1502.70,113.01],[1505.64,129.03],[1508.26,145.91],[1493.64,149.92],[1476.55,149.92],[1459.45,149.92],[1442.36,149.92],[1425.27,149.92],[1408.17,149.92],[1391.08,149.92]]
];
wl_piece_mask = [
  [[-18.00,-23.89],[-18.00,275.12],[252.00,286.12],[252.00,285.12],[252.00,284.12],[252.00,283.12],[252.00,281.12],[252.00,279.12],[252.00,277.12],[252.00,275.12],[252.00,273.12],[252.00,271.12],[252.00,269.12],[252.00,267.12],[252.00,265.12],[252.00,263.12],[252.00,261.12],[252.00,259.12],[252.00,257.12],[252.29,255.12],[252.86,253.12],[253.71,251.12],[254.86,249.12],[256.29,247.12],[258.00,245.12],[260.00,243.12],[262.00,241.12],[264.00,239.12],[266.00,237.12],[268.00,235.12],[270.00,233.12],[271.71,231.12],[273.43,229.12],[274.86,227.12],[276.00,225.12],[276.86,223.12],[277.43,221.12],[277.71,219.12],[278.00,217.12],[278.00,215.12],[278.00,213.12],[278.00,211.12],[277.71,209.12],[277.14,207.12],[276.29,205.12],[275.14,203.12],[273.71,201.12],[272.00,199.12],[270.00,197.12],[268.00,195.12],[266.00,193.12],[264.00,191.12],[262.00,189.12],[260.00,187.12],[258.00,185.12],[256.29,183.12],[254.57,181.12],[253.14,179.12],[252.00,177.12],[251.14,175.12],[250.29,173.12],[249.71,171.12],[249.14,169.12],[248.86,167.12],[248.57,165.12],[248.29,163.12],[247.71,161.12],[247.43,159.12],[247.14,157.12],[246.86,155.12],[246.57,153.12],[246.29,151.12],[245.71,149.12],[245.43,147.12],[245.14,145.12],[244.86,143.12],[244.57,141.12],[244.00,139.12],[243.43,137.12],[243.14,135.12],[242.86,133.12],[242.57,131.12],[242.00,129.12],[241.43,127.12],[241.14,125.11],[240.86,123.11],[240.57,121.11],[240.29,119.11],[239.71,117.11],[239.43,115.11],[239.14,113.11],[238.86,111.11],[238.57,109.11],[238.29,107.11],[237.71,105.11],[237.43,103.11],[237.14,101.11],[236.86,99.11],[236.57,97.11],[236.29,95.11],[235.71,93.11],[235.43,91.11],[235.14,89.11],[234.86,87.11],[234.57,85.11],[234.00,83.11],[233.43,81.11],[233.14,79.11],[232.86,77.11],[232.57,75.11],[232.29,73.11],[231.71,71.11],[231.43,69.11],[231.14,67.11],[230.86,65.11],[230.57,63.11],[230.29,61.11],[229.71,59.11],[229.43,57.11],[229.14,55.11],[228.86,53.11],[228.57,51.11],[228.29,49.11],[227.71,47.11],[227.43,45.11],[227.14,43.11],[226.86,41.11],[226.57,39.11],[226.29,37.11],[225.71,35.11],[225.43,33.11],[225.14,31.11],[224.86,29.11],[224.57,27.11],[224.29,25.11],[224.00,23.11],[224.00,21.11],[224.00,19.11],[224.00,17.11],[224.00,15.11],[224.00,13.11],[224.00,11.11],[224.00,9.11],[224.29,7.11],[224.86,5.11],[225.71,3.11],[226.86,1.11],[228.29,-0.89],[230.00,-2.89],[232.00,-4.89],[234.00,-6.89],[236.00,-8.89],[238.00,-10.89],[240.00,-12.89],[242.00,-14.89],[244.00,-16.89],[246.00,-18.89],[247.71,-20.89],[249.14,-22.89],[250.29,-24.89],[251.14,-26.89],[251.71,-28.89],[252.00,-29.89],[252.00,-30.89],[252.00,-31.89]],
  [[252.00,-31.89],[252.00,-30.89],[252.00,-29.89],[251.71,-28.89],[251.14,-26.89],[250.29,-24.89],[249.14,-22.89],[247.71,-20.89],[246.00,-18.89],[244.00,-16.89],[242.00,-14.89],[240.00,-12.89],[238.00,-10.89],[236.00,-8.89],[234.00,-6.89],[232.00,-4.89],[230.00,-2.89],[228.29,-0.89],[226.86,1.11],[225.71,3.11],[224.86,5.11],[224.29,7.11],[224.00,9.11],[224.00,11.11],[224.00,13.11],[224.00,15.11],[224.00,17.11],[224.00,19.11],[224.00,21.11],[224.00,23.11],[224.29,25.11],[224.57,27.11],[224.86,29.11],[225.14,31.11],[225.43,33.11],[225.71,35.11],[226.29,37.11],[226.57,39.11],[226.86,41.11],[227.14,43.11],[227.43,45.11],[227.71,47.11],[228.29,49.11],[228.57,51.11],[228.86,53.11],[229.14,55.11],[229.43,57.11],[229.71,59.11],[230.29,61.11],[230.57,63.11],[230.86,65.11],[231.14,67.11],[231.43,69.11],[231.71,71.11],[232.29,73.11],[232.57,75.11],[232.86,77.11],[233.14,79.11],[233.43,81.11],[234.00,83.11],[234.57,85.11],[234.86,87.11],[235.14,89.11],[235.43,91.11],[235.71,93.11],[236.29,95.11],[236.57,97.11],[236.86,99.11],[237.14,101.11],[237.43,103.11],[237.71,105.11],[238.29,107.11],[238.57,109.11],[238.86,111.11],[239.14,113.11],[239.43,115.11],[239.71,117.11],[240.29,119.11],[240.57,121.11],[240.86,123.11],[241.14,125.11],[241.43,127.12],[242.00,129.12],[242.57,131.12],[242.86,133.12],[243.14,135.12],[243.43,137.12],[244.00,139.12],[244.57,141.12],[244.86,143.12],[245.14,145.12],[245.43,147.12],[245.71,149.12],[246.29,151.12],[246.57,153.12],[246.86,155.12],[247.14,157.12],[247.43,159.12],[247.71,161.12],[248.29,163.12],[248.57,165.12],[248.86,167.12],[249.14,169.12],[249.71,171.12],[250.29,173.12],[251.14,175.12],[252.00,177.12],[253.14,179.12],[254.57,181.12],[256.29,183.12],[258.00,185.12],[260.00,187.12],[262.00,189.12],[264.00,191.12],[266.00,193.12],[268.00,195.12],[270.00,197.12],[272.00,199.12],[273.71,201.12],[275.14,203.12],[276.29,205.12],[277.14,207.12],[277.71,209.12],[278.00,211.12],[278.00,213.12],[278.00,215.12],[278.00,217.12],[277.71,219.12],[277.43,221.12],[276.86,223.12],[276.00,225.12],[274.86,227.12],[273.43,229.12],[271.71,231.12],[270.00,233.12],[268.00,235.12],[266.00,237.12],[264.00,239.12],[262.00,241.12],[260.00,243.12],[258.00,245.12],[256.29,247.12],[254.86,249.12],[253.71,251.12],[252.86,253.12],[252.29,255.12],[252.00,257.12],[252.00,259.12],[252.00,261.12],[252.00,263.12],[252.00,265.12],[252.00,267.12],[252.00,269.12],[252.00,271.12],[252.00,273.12],[252.00,275.12],[252.00,277.12],[252.00,279.12],[252.00,281.12],[252.00,283.12],[252.00,284.12],[252.00,285.12],[252.00,286.12],[504.00,286.12],[504.00,285.12],[504.33,284.12],[504.86,283.12],[505.71,281.12],[506.86,279.12],[508.29,277.12],[510.00,275.12],[512.00,273.12],[514.00,271.12],[516.00,269.12],[518.00,267.12],[520.00,265.12],[522.00,263.12],[524.00,261.12],[526.00,259.12],[528.00,257.12],[530.00,255.12],[532.00,253.12],[534.00,251.12],[535.71,249.12],[537.14,247.12],[538.29,245.12],[539.14,243.12],[539.71,241.12],[540.00,239.12],[540.00,237.12],[540.00,235.12],[540.00,233.12],[540.00,231.12],[539.71,229.12],[539.43,227.12],[539.14,225.12],[538.86,223.12],[538.57,221.12],[538.29,219.12],[537.71,217.12],[537.43,215.12],[537.14,213.12],[536.86,211.12],[536.57,209.12],[536.00,207.12],[535.43,205.12],[535.14,203.12],[534.86,201.12],[534.57,199.12],[534.29,197.12],[533.71,195.12],[533.43,193.12],[533.14,191.12],[532.86,189.12],[532.57,187.12],[532.00,185.12],[531.43,183.12],[531.14,181.12],[530.57,179.12],[529.71,177.12],[528.57,175.12],[527.14,173.12],[525.71,171.12],[524.00,169.12],[522.00,167.12],[520.00,165.12],[518.00,163.12],[516.00,161.12],[514.00,159.12],[512.00,157.12],[510.00,155.12],[508.29,153.12],[506.86,151.12],[505.71,149.12],[504.86,147.12],[504.29,145.12],[504.00,143.12],[504.00,141.12],[504.00,139.12],[504.00,137.12],[504.00,135.12],[504.00,133.12],[504.00,131.12],[504.00,129.12],[504.00,127.12],[504.00,125.11],[504.00,123.11],[504.00,121.11],[504.00,119.11],[504.00,117.11],[504.00,115.11],[504.00,113.11],[504.00,111.11],[504.00,109.11],[504.00,107.11],[504.00,105.11],[504.00,103.11],[504.00,101.11],[504.00,99.11],[504.00,97.11],[504.00,95.11],[504.00,93.11],[504.00,91.11],[504.00,89.11],[504.00,87.11],[503.71,85.11],[503.43,83.11],[503.14,81.11],[502.57,79.11],[502.00,77.11],[501.14,75.11],[500.00,73.11],[498.86,71.11],[497.71,69.11],[496.29,67.11],[495.14,65.11],[493.71,63.11],[492.29,61.11],[491.14,59.11],[490.00,57.11],[488.86,55.11],[487.71,53.11],[486.29,51.11],[485.14,49.11],[484.00,47.11],[482.86,45.11],[481.71,43.11],[480.29,41.11],[478.86,39.11],[477.71,37.11],[476.57,35.11],[475.43,33.11],[474.29,31.11],[473.14,29.11],[472.29,27.11],[471.43,25.11],[470.57,23.11],[469.71,21.11],[469.14,19.11],[468.57,17.11],[468.29,15.11],[468.00,13.11],[468.00,11.11],[468.00,9.11],[468.29,7.11],[468.86,5.11],[469.71,3.11],[470.86,1.11],[472.29,-0.89],[474.00,-2.89],[476.00,-4.89],[478.00,-6.89],[480.00,-8.89],[482.00,-10.89],[484.00,-12.89],[486.00,-14.89],[488.00,-16.89],[490.00,-18.89],[492.00,-20.89],[494.00,-22.89],[495.71,-24.89],[497.14,-26.89],[498.29,-28.89],[499.00,-29.89],[499.60,-30.89],[500.00,-31.89]],
  [[500.00,-31.89],[499.60,-30.89],[499.00,-29.89],[498.29,-28.89],[497.14,-26.89],[495.71,-24.89],[494.00,-22.89],[492.00,-20.89],[490.00,-18.89],[488.00,-16.89],[486.00,-14.89],[484.00,-12.89],[482.00,-10.89],[480.00,-8.89],[478.00,-6.89],[476.00,-4.89],[474.00,-2.89],[472.29,-0.89],[470.86,1.11],[469.71,3.11],[468.86,5.11],[468.29,7.11],[468.00,9.11],[468.00,11.11],[468.00,13.11],[468.29,15.11],[468.57,17.11],[469.14,19.11],[469.71,21.11],[470.57,23.11],[471.43,25.11],[472.29,27.11],[473.14,29.11],[474.29,31.11],[475.43,33.11],[476.57,35.11],[477.71,37.11],[478.86,39.11],[480.29,41.11],[481.71,43.11],[482.86,45.11],[484.00,47.11],[485.14,49.11],[486.29,51.11],[487.71,53.11],[488.86,55.11],[490.00,57.11],[491.14,59.11],[492.29,61.11],[493.71,63.11],[495.14,65.11],[496.29,67.11],[497.71,69.11],[498.86,71.11],[500.00,73.11],[501.14,75.11],[502.00,77.11],[502.57,79.11],[503.14,81.11],[503.43,83.11],[503.71,85.11],[504.00,87.11],[504.00,89.11],[504.00,91.11],[504.00,93.11],[504.00,95.11],[504.00,97.11],[504.00,99.11],[504.00,101.11],[504.00,103.11],[504.00,105.11],[504.00,107.11],[504.00,109.11],[504.00,111.11],[504.00,113.11],[504.00,115.11],[504.00,117.11],[504.00,119.11],[504.00,121.11],[504.00,123.11],[504.00,125.11],[504.00,127.12],[504.00,129.12],[504.00,131.12],[504.00,133.12],[504.00,135.12],[504.00,137.12],[504.00,139.12],[504.00,141.12],[504.00,143.12],[504.29,145.12],[504.86,147.12],[505.71,149.12],[506.86,151.12],[508.29,153.12],[510.00,155.12],[512.00,157.12],[514.00,159.12],[516.00,161.12],[518.00,163.12],[520.00,165.12],[522.00,167.12],[524.00,169.12],[525.71,171.12],[527.14,173.12],[528.57,175.12],[529.71,177.12],[530.57,179.12],[531.14,181.12],[531.43,183.12],[532.00,185.12],[532.57,187.12],[532.86,189.12],[533.14,191.12],[533.43,193.12],[533.71,195.12],[534.29,197.12],[534.57,199.12],[534.86,201.12],[535.14,203.12],[535.43,205.12],[536.00,207.12],[536.57,209.12],[536.86,211.12],[537.14,213.12],[537.43,215.12],[537.71,217.12],[538.29,219.12],[538.57,221.12],[538.86,223.12],[539.14,225.12],[539.43,227.12],[539.71,229.12],[540.00,231.12],[540.00,233.12],[540.00,235.12],[540.00,237.12],[540.00,239.12],[539.71,241.12],[539.14,243.12],[538.29,245.12],[537.14,247.12],[535.71,249.12],[534.00,251.12],[532.00,253.12],[530.00,255.12],[528.00,257.12],[526.00,259.12],[524.00,261.12],[522.00,263.12],[520.00,265.12],[518.00,267.12],[516.00,269.12],[514.00,271.12],[512.00,273.12],[510.00,275.12],[508.29,277.12],[506.86,279.12],[505.71,281.12],[504.86,283.12],[504.33,284.12],[504.00,285.12],[504.00,286.12],[764.00,286.12],[764.00,285.12],[764.00,284.12],[764.00,283.12],[764.00,281.12],[764.00,279.12],[764.00,277.12],[764.00,275.12],[764.00,273.12],[764.00,271.12],[764.00,269.12],[764.00,267.12],[764.00,265.12],[764.00,263.12],[764.00,261.12],[764.00,259.12],[764.00,257.12],[764.00,255.12],[764.00,253.12],[764.00,251.12],[764.00,249.12],[764.00,247.12],[764.00,245.12],[764.00,243.12],[764.00,241.12],[764.00,239.12],[764.00,237.12],[764.00,235.12],[764.00,233.12],[764.00,231.12],[764.00,229.12],[764.00,227.12],[764.00,225.12],[764.00,223.12],[764.00,221.12],[764.00,219.12],[764.00,217.12],[764.00,215.12],[764.00,213.12],[764.00,211.12],[764.00,209.12],[764.00,207.12],[764.00,205.12],[764.00,203.12],[764.00,201.12],[764.00,199.12],[764.00,197.12],[764.00,195.12],[764.00,193.12],[764.00,191.12],[764.00,189.12],[764.00,187.12],[764.00,185.12],[764.00,183.12],[764.00,181.12],[764.00,179.12],[764.00,177.12],[764.00,175.12],[764.00,173.12],[764.00,171.12],[764.00,169.12],[764.00,167.12],[764.00,165.12],[764.00,163.12],[764.00,161.12],[764.00,159.12],[764.00,157.12],[764.00,155.12],[764.00,153.12],[764.00,151.12],[764.00,149.12],[764.00,147.12],[764.00,145.12],[764.00,143.12],[764.00,141.12],[764.00,139.12],[764.00,137.12],[764.00,135.12],[764.00,133.12],[764.00,131.12],[764.00,129.12],[764.00,127.12],[764.00,125.11],[764.00,123.11],[764.00,121.11],[764.00,119.11],[764.00,117.11],[764.00,115.11],[764.00,113.11],[764.00,111.11],[764.00,109.11],[764.00,107.11],[764.00,105.11],[764.00,103.11],[764.00,101.11],[764.00,99.11],[764.00,97.11],[764.00,95.11],[764.00,93.11],[764.00,91.11],[764.00,89.11],[764.00,87.11],[764.00,85.11],[764.00,83.11],[764.00,81.11],[764.00,79.11],[764.00,77.11],[764.00,75.11],[764.00,73.11],[764.00,71.11],[764.00,69.11],[764.00,67.11],[764.00,65.11],[764.00,63.11],[764.00,61.11],[764.00,59.11],[764.00,57.11],[764.00,55.11],[764.00,53.11],[764.00,51.11],[764.00,49.11],[764.00,47.11],[764.00,45.11],[764.00,43.11],[764.00,41.11],[764.00,39.11],[764.00,37.11],[764.00,35.11],[764.00,33.11],[764.00,31.11],[764.00,29.11],[764.00,27.11],[764.00,25.11],[764.00,23.11],[764.00,21.11],[764.00,19.11],[764.00,17.11],[764.00,15.11],[764.00,13.11],[764.00,11.11],[764.00,9.11],[764.00,7.11],[764.00,5.11],[764.00,3.11],[764.00,1.11],[764.00,-0.89],[764.00,-2.89],[764.00,-4.89],[764.00,-6.89],[764.00,-8.89],[764.00,-10.89],[764.00,-12.89],[764.00,-14.89],[764.00,-16.89],[764.00,-18.89],[764.00,-20.89],[764.00,-22.89],[764.00,-24.89],[764.00,-26.89],[764.00,-28.89],[764.00,-29.89],[764.00,-30.89],[764.00,-31.89]],
  [[764.00,-31.89],[764.00,-30.89],[764.00,-29.89],[764.00,-28.89],[764.00,-26.89],[764.00,-24.89],[764.00,-22.89],[764.00,-20.89],[764.00,-18.89],[764.00,-16.89],[764.00,-14.89],[764.00,-12.89],[764.00,-10.89],[764.00,-8.89],[764.00,-6.89],[764.00,-4.89],[764.00,-2.89],[764.00,-0.89],[764.00,1.11],[764.00,3.11],[764.00,5.11],[764.00,7.11],[764.00,9.11],[764.00,11.11],[764.00,13.11],[764.00,15.11],[764.00,17.11],[764.00,19.11],[764.00,21.11],[764.00,23.11],[764.00,25.11],[764.00,27.11],[764.00,29.11],[764.00,31.11],[764.00,33.11],[764.00,35.11],[764.00,37.11],[764.00,39.11],[764.00,41.11],[764.00,43.11],[764.00,45.11],[764.00,47.11],[764.00,49.11],[764.00,51.11],[764.00,53.11],[764.00,55.11],[764.00,57.11],[764.00,59.11],[764.00,61.11],[764.00,63.11],[764.00,65.11],[764.00,67.11],[764.00,69.11],[764.00,71.11],[764.00,73.11],[764.00,75.11],[764.00,77.11],[764.00,79.11],[764.00,81.11],[764.00,83.11],[764.00,85.11],[764.00,87.11],[764.00,89.11],[764.00,91.11],[764.00,93.11],[764.00,95.11],[764.00,97.11],[764.00,99.11],[764.00,101.11],[764.00,103.11],[764.00,105.11],[764.00,107.11],[764.00,109.11],[764.00,111.11],[764.00,113.11],[764.00,115.11],[764.00,117.11],[764.00,119.11],[764.00,121.11],[764.00,123.11],[764.00,125.11],[764.00,127.12],[764.00,129.12],[764.00,131.12],[764.00,133.12],[764.00,135.12],[764.00,137.12],[764.00,139.12],[764.00,141.12],[764.00,143.12],[764.00,145.12],[764.00,147.12],[764.00,149.12],[764.00,151.12],[764.00,153.12],[764.00,155.12],[764.00,157.12],[764.00,159.12],[764.00,161.12],[764.00,163.12],[764.00,165.12],[764.00,167.12],[764.00,169.12],[764.00,171.12],[764.00,173.12],[764.00,175.12],[764.00,177.12],[764.00,179.12],[764.00,181.12],[764.00,183.12],[764.00,185.12],[764.00,187.12],[764.00,189.12],[764.00,191.12],[764.00,193.12],[764.00,195.12],[764.00,197.12],[764.00,199.12],[764.00,201.12],[764.00,203.12],[764.00,205.12],[764.00,207.12],[764.00,209.12],[764.00,211.12],[764.00,213.12],[764.00,215.12],[764.00,217.12],[764.00,219.12],[764.00,221.12],[764.00,223.12],[764.00,225.12],[764.00,227.12],[764.00,229.12],[764.00,231.12],[764.00,233.12],[764.00,235.12],[764.00,237.12],[764.00,239.12],[764.00,241.12],[764.00,243.12],[764.00,245.12],[764.00,247.12],[764.00,249.12],[764.00,251.12],[764.00,253.12],[764.00,255.12],[764.00,257.12],[764.00,259.12],[764.00,261.12],[764.00,263.12],[764.00,265.12],[764.00,267.12],[764.00,269.12],[764.00,271.12],[764.00,273.12],[764.00,275.12],[764.00,277.12],[764.00,279.12],[764.00,281.12],[764.00,283.12],[764.00,284.12],[764.00,285.12],[764.00,286.12],[1050.00,286.12],[1050.00,285.12],[1050.00,284.12],[1050.00,283.12],[1050.00,281.12],[1050.00,279.12],[1050.00,277.12],[1050.00,275.12],[1050.00,273.12],[1050.00,271.12],[1050.00,269.12],[1050.00,267.12],[1050.00,265.12],[1050.00,263.12],[1050.00,261.12],[1050.00,259.12],[1050.00,257.12],[1050.00,255.12],[1050.00,253.12],[1050.00,251.12],[1050.00,249.12],[1050.00,247.12],[1050.00,245.12],[1050.00,243.12],[1050.00,241.12],[1050.00,239.12],[1050.00,237.12],[1050.00,235.12],[1050.00,233.12],[1050.00,231.12],[1050.00,229.12],[1050.00,227.12],[1050.00,225.12],[1050.00,223.12],[1050.00,221.12],[1050.00,219.12],[1050.29,217.12],[1050.57,215.12],[1051.14,213.12],[1051.71,211.12],[1052.29,209.12],[1053.14,207.12],[1054.00,205.12],[1054.57,203.12],[1055.14,201.12],[1055.43,199.12],[1055.71,197.12],[1056.00,195.12],[1056.00,193.12],[1056.00,191.12],[1056.00,189.12],[1056.00,187.12],[1056.00,185.12],[1055.71,183.12],[1055.43,181.12],[1055.14,179.12],[1054.57,177.12],[1054.00,175.12],[1053.14,173.12],[1052.29,171.12],[1051.43,169.12],[1050.57,167.12],[1049.43,165.12],[1048.57,163.12],[1047.71,161.12],[1047.14,159.12],[1046.29,157.12],[1045.71,155.12],[1045.14,153.12],[1044.57,151.12],[1044.00,149.12],[1043.43,147.12],[1042.86,145.12],[1042.57,143.12],[1042.29,141.12],[1041.71,139.12],[1041.43,137.12],[1041.14,135.12],[1040.86,133.12],[1040.57,131.12],[1040.29,129.12],[1040.00,127.12],[1040.00,125.11],[1040.00,123.11],[1040.00,121.11],[1040.00,119.11],[1040.00,117.11],[1040.00,115.11],[1040.00,113.11],[1040.00,111.11],[1040.00,109.11],[1040.00,107.11],[1040.00,105.11],[1040.00,103.11],[1040.00,101.11],[1040.00,99.11],[1040.00,97.11],[1040.00,95.11],[1040.00,93.11],[1040.00,91.11],[1040.00,89.11],[1040.00,87.11],[1040.00,85.11],[1040.00,83.11],[1040.29,81.11],[1040.57,79.11],[1040.86,77.11],[1041.14,75.11],[1041.71,73.11],[1042.29,71.11],[1042.86,69.11],[1043.43,67.11],[1044.00,65.11],[1044.57,63.11],[1045.43,61.11],[1046.00,59.11],[1046.57,57.11],[1047.14,55.11],[1047.43,53.11],[1048.00,51.11],[1048.57,49.11],[1048.86,47.11],[1049.14,45.11],[1049.43,43.11],[1049.71,41.11],[1050.00,39.11],[1050.00,37.11],[1050.00,35.11],[1050.00,33.11],[1050.00,31.11],[1050.00,29.11],[1050.00,27.11],[1050.00,25.11],[1050.00,23.11],[1050.00,21.11],[1050.00,19.11],[1050.00,17.11],[1050.00,15.11],[1050.00,13.11],[1050.00,11.11],[1050.00,9.11],[1050.00,7.11],[1050.00,5.11],[1050.00,3.11],[1050.00,1.11],[1050.00,-0.89],[1050.00,-2.89],[1050.00,-4.89],[1050.00,-6.89],[1050.00,-8.89],[1050.00,-10.89],[1050.00,-12.89],[1050.00,-14.89],[1050.00,-16.89],[1050.00,-18.89],[1050.00,-20.89],[1050.00,-22.89],[1050.00,-24.89],[1050.00,-26.89],[1050.00,-28.89],[1050.00,-29.89],[1050.00,-30.89],[1050.00,-31.89]],
  [[1050.00,-31.89],[1050.00,-30.89],[1050.00,-29.89],[1050.00,-28.89],[1050.00,-26.89],[1050.00,-24.89],[1050.00,-22.89],[1050.00,-20.89],[1050.00,-18.89],[1050.00,-16.89],[1050.00,-14.89],[1050.00,-12.89],[1050.00,-10.89],[1050.00,-8.89],[1050.00,-6.89],[1050.00,-4.89],[1050.00,-2.89],[1050.00,-0.89],[1050.00,1.11],[1050.00,3.11],[1050.00,5.11],[1050.00,7.11],[1050.00,9.11],[1050.00,11.11],[1050.00,13.11],[1050.00,15.11],[1050.00,17.11],[1050.00,19.11],[1050.00,21.11],[1050.00,23.11],[1050.00,25.11],[1050.00,27.11],[1050.00,29.11],[1050.00,31.11],[1050.00,33.11],[1050.00,35.11],[1050.00,37.11],[1050.00,39.11],[1049.71,41.11],[1049.43,43.11],[1049.14,45.11],[1048.86,47.11],[1048.57,49.11],[1048.00,51.11],[1047.43,53.11],[1047.14,55.11],[1046.57,57.11],[1046.00,59.11],[1045.43,61.11],[1044.57,63.11],[1044.00,65.11],[1043.43,67.11],[1042.86,69.11],[1042.29,71.11],[1041.71,73.11],[1041.14,75.11],[1040.86,77.11],[1040.57,79.11],[1040.29,81.11],[1040.00,83.11],[1040.00,85.11],[1040.00,87.11],[1040.00,89.11],[1040.00,91.11],[1040.00,93.11],[1040.00,95.11],[1040.00,97.11],[1040.00,99.11],[1040.00,101.11],[1040.00,103.11],[1040.00,105.11],[1040.00,107.11],[1040.00,109.11],[1040.00,111.11],[1040.00,113.11],[1040.00,115.11],[1040.00,117.11],[1040.00,119.11],[1040.00,121.11],[1040.00,123.11],[1040.00,125.11],[1040.00,127.12],[1040.29,129.12],[1040.57,131.12],[1040.86,133.12],[1041.14,135.12],[1041.43,137.12],[1041.71,139.12],[1042.29,141.12],[1042.57,143.12],[1042.86,145.12],[1043.43,147.12],[1044.00,149.12],[1044.57,151.12],[1045.14,153.12],[1045.71,155.12],[1046.29,157.12],[1047.14,159.12],[1047.71,161.12],[1048.57,163.12],[1049.43,165.12],[1050.57,167.12],[1051.43,169.12],[1052.29,171.12],[1053.14,173.12],[1054.00,175.12],[1054.57,177.12],[1055.14,179.12],[1055.43,181.12],[1055.71,183.12],[1056.00,185.12],[1056.00,187.12],[1056.00,189.12],[1056.00,191.12],[1056.00,193.12],[1056.00,195.12],[1055.71,197.12],[1055.43,199.12],[1055.14,201.12],[1054.57,203.12],[1054.00,205.12],[1053.14,207.12],[1052.29,209.12],[1051.71,211.12],[1051.14,213.12],[1050.57,215.12],[1050.29,217.12],[1050.00,219.12],[1050.00,221.12],[1050.00,223.12],[1050.00,225.12],[1050.00,227.12],[1050.00,229.12],[1050.00,231.12],[1050.00,233.12],[1050.00,235.12],[1050.00,237.12],[1050.00,239.12],[1050.00,241.12],[1050.00,243.12],[1050.00,245.12],[1050.00,247.12],[1050.00,249.12],[1050.00,251.12],[1050.00,253.12],[1050.00,255.12],[1050.00,257.12],[1050.00,259.12],[1050.00,261.12],[1050.00,263.12],[1050.00,265.12],[1050.00,267.12],[1050.00,269.12],[1050.00,271.12],[1050.00,273.12],[1050.00,275.12],[1050.00,277.12],[1050.00,279.12],[1050.00,281.12],[1050.00,283.12],[1050.00,284.12],[1050.00,285.12],[1050.00,286.12],[1316.00,286.12],[1316.00,285.12],[1316.00,284.12],[1316.00,283.12],[1316.00,281.12],[1316.00,279.12],[1316.00,277.12],[1316.00,275.12],[1316.00,273.12],[1316.00,271.12],[1316.00,269.12],[1316.00,267.12],[1316.00,265.12],[1316.00,263.12],[1316.00,261.12],[1316.00,259.12],[1316.00,257.12],[1316.00,255.12],[1316.29,253.12],[1316.86,251.12],[1317.71,249.12],[1318.86,247.12],[1320.29,245.12],[1322.00,243.12],[1324.00,241.12],[1326.00,239.12],[1328.00,237.12],[1330.00,235.12],[1332.00,233.12],[1333.71,231.12],[1335.43,229.12],[1336.86,227.12],[1338.00,225.12],[1338.86,223.12],[1339.43,221.12],[1339.71,219.12],[1340.00,217.12],[1340.00,215.12],[1340.00,213.12],[1339.71,211.12],[1339.43,209.12],[1339.14,207.12],[1338.57,205.12],[1337.71,203.12],[1336.57,201.12],[1335.14,199.12],[1333.71,197.12],[1332.00,195.12],[1330.00,193.12],[1328.00,191.12],[1326.00,189.12],[1324.00,187.12],[1322.29,185.12],[1320.57,183.12],[1319.14,181.12],[1318.00,179.12],[1317.14,177.12],[1316.57,175.12],[1316.29,173.12],[1316.00,171.12],[1316.00,169.12],[1315.71,167.12],[1315.43,165.12],[1315.14,163.12],[1314.86,161.12],[1314.57,159.12],[1314.00,157.12],[1313.43,155.12],[1313.14,153.12],[1312.86,151.12],[1312.57,149.12],[1312.00,147.12],[1311.43,145.12],[1311.14,143.12],[1310.86,141.12],[1310.57,139.12],[1310.29,137.12],[1309.71,135.12],[1309.43,133.12],[1309.14,131.12],[1308.86,129.12],[1308.57,127.12],[1308.29,125.11],[1307.71,123.11],[1307.43,121.11],[1307.14,119.11],[1306.86,117.11],[1306.57,115.11],[1306.00,113.11],[1305.43,111.11],[1305.14,109.11],[1304.86,107.11],[1304.57,105.11],[1304.29,103.11],[1303.71,101.11],[1303.43,99.11],[1303.14,97.11],[1302.86,95.11],[1302.57,93.11],[1302.29,91.11],[1301.71,89.11],[1301.43,87.11],[1301.14,85.11],[1300.86,83.11],[1300.57,81.11],[1300.29,79.11],[1299.71,77.11],[1299.43,75.11],[1299.14,73.11],[1298.86,71.11],[1298.57,69.11],[1298.29,67.11],[1297.71,65.11],[1297.43,63.11],[1297.14,61.11],[1296.86,59.11],[1296.57,57.11],[1296.00,55.11],[1295.43,53.11],[1295.14,51.11],[1294.86,49.11],[1294.57,47.11],[1294.29,45.11],[1293.71,43.11],[1293.43,41.11],[1293.14,39.11],[1292.86,37.11],[1292.57,35.11],[1292.29,33.11],[1291.71,31.11],[1291.43,29.11],[1291.14,27.11],[1290.86,25.11],[1290.57,23.11],[1290.29,21.11],[1290.00,19.11],[1290.00,17.11],[1290.00,15.11],[1290.00,13.11],[1290.00,11.11],[1290.29,9.11],[1290.57,7.11],[1290.86,5.11],[1291.43,3.11],[1292.29,1.11],[1293.43,-0.89],[1294.86,-2.89],[1296.29,-4.89],[1298.00,-6.89],[1300.00,-8.89],[1302.00,-10.89],[1304.00,-12.89],[1306.00,-14.89],[1308.00,-16.89],[1310.00,-18.89],[1311.71,-20.89],[1313.14,-22.89],[1314.29,-24.89],[1315.14,-26.89],[1315.71,-28.89],[1316.00,-29.89],[1316.00,-30.89],[1316.00,-31.89]],
  [[1316.00,-31.89],[1316.00,-30.89],[1316.00,-29.89],[1315.71,-28.89],[1315.14,-26.89],[1314.29,-24.89],[1313.14,-22.89],[1311.71,-20.89],[1310.00,-18.89],[1308.00,-16.89],[1306.00,-14.89],[1304.00,-12.89],[1302.00,-10.89],[1300.00,-8.89],[1298.00,-6.89],[1296.29,-4.89],[1294.86,-2.89],[1293.43,-0.89],[1292.29,1.11],[1291.43,3.11],[1290.86,5.11],[1290.57,7.11],[1290.29,9.11],[1290.00,11.11],[1290.00,13.11],[1290.00,15.11],[1290.00,17.11],[1290.00,19.11],[1290.29,21.11],[1290.57,23.11],[1290.86,25.11],[1291.14,27.11],[1291.43,29.11],[1291.71,31.11],[1292.29,33.11],[1292.57,35.11],[1292.86,37.11],[1293.14,39.11],[1293.43,41.11],[1293.71,43.11],[1294.29,45.11],[1294.57,47.11],[1294.86,49.11],[1295.14,51.11],[1295.43,53.11],[1296.00,55.11],[1296.57,57.11],[1296.86,59.11],[1297.14,61.11],[1297.43,63.11],[1297.71,65.11],[1298.29,67.11],[1298.57,69.11],[1298.86,71.11],[1299.14,73.11],[1299.43,75.11],[1299.71,77.11],[1300.29,79.11],[1300.57,81.11],[1300.86,83.11],[1301.14,85.11],[1301.43,87.11],[1301.71,89.11],[1302.29,91.11],[1302.57,93.11],[1302.86,95.11],[1303.14,97.11],[1303.43,99.11],[1303.71,101.11],[1304.29,103.11],[1304.57,105.11],[1304.86,107.11],[1305.14,109.11],[1305.43,111.11],[1306.00,113.11],[1306.57,115.11],[1306.86,117.11],[1307.14,119.11],[1307.43,121.11],[1307.71,123.11],[1308.29,125.11],[1308.57,127.12],[1308.86,129.12],[1309.14,131.12],[1309.43,133.12],[1309.71,135.12],[1310.29,137.12],[1310.57,139.12],[1310.86,141.12],[1311.14,143.12],[1311.43,145.12],[1312.00,147.12],[1312.57,149.12],[1312.86,151.12],[1313.14,153.12],[1313.43,155.12],[1314.00,157.12],[1314.57,159.12],[1314.86,161.12],[1315.14,163.12],[1315.43,165.12],[1315.71,167.12],[1316.00,169.12],[1316.00,171.12],[1316.29,173.12],[1316.57,175.12],[1317.14,177.12],[1318.00,179.12],[1319.14,181.12],[1320.57,183.12],[1322.29,185.12],[1324.00,187.12],[1326.00,189.12],[1328.00,191.12],[1330.00,193.12],[1332.00,195.12],[1333.71,197.12],[1335.14,199.12],[1336.57,201.12],[1337.71,203.12],[1338.57,205.12],[1339.14,207.12],[1339.43,209.12],[1339.71,211.12],[1340.00,213.12],[1340.00,215.12],[1340.00,217.12],[1339.71,219.12],[1339.43,221.12],[1338.86,223.12],[1338.00,225.12],[1336.86,227.12],[1335.43,229.12],[1333.71,231.12],[1332.00,233.12],[1330.00,235.12],[1328.00,237.12],[1326.00,239.12],[1324.00,241.12],[1322.00,243.12],[1320.29,245.12],[1318.86,247.12],[1317.71,249.12],[1316.86,251.12],[1316.29,253.12],[1316.00,255.12],[1316.00,257.12],[1316.00,259.12],[1316.00,261.12],[1316.00,263.12],[1316.00,265.12],[1316.00,267.12],[1316.00,269.12],[1316.00,271.12],[1316.00,273.12],[1316.00,275.12],[1316.00,277.12],[1316.00,279.12],[1316.00,281.12],[1316.00,283.12],[1316.00,284.12],[1316.00,285.12],[1316.00,286.12],[1581.25,275.12],[1581.25,-23.89]]
];
wl_piece_scr = [
  [[-5.00,-15.90],[113.50,-15.90],[232.00,-15.90],[-5.00,267.10],[117.50,267.10],[240.00,267.10]],
  [[256.00,-15.90],[366.00,-15.90],[476.00,-15.90],[264.00,267.10],[385.00,267.10],[506.00,267.10]],
  [[500.00,-15.90],[626.00,-15.90],[752.00,-15.90],[530.00,267.10],[641.00,267.10],[752.00,267.10]],
  [[776.00,-15.90],[907.00,-15.90],[1038.00,-15.90],[776.00,267.10],[907.00,267.10],[1038.00,267.10]],
  [[1062.00,-15.90],[1179.00,-15.90],[1296.00,-15.90],[1062.00,267.10],[1183.00,267.10],[1304.00,267.10]],
  [[1320.00,-15.90],[1444.10,-15.90],[1568.20,-15.90],[1328.00,267.10],[1448.10,267.10],[1568.20,267.10]]
];
wl_piece_tie = [
  [],
  [],
  [],
  [],
  [],
  []
];
wl_labels = ["1C","2H","3A","4R","5G","6E"];
wl_centers = [[130.5,125.6],[382.0,125.6],[616.0,125.6],[910.0,125.6],[1190.0,125.6],[1435.1,125.6]];
